mlukasek/SAPI_DTR-1/SW/PSoC_Creator/DTR-1 v2 HW.cydsn/codegentemp/AddrH.h

/*******************************************************************************
* File Name: AddrH.h  
* Version 2.20
*
* Description:
*  This file contains Pin function prototypes and register defines
*
* Note:
*
********************************************************************************
* Copyright 2008-2015, Cypress Semiconductor Corporation.  All rights reserved.
* You may use this file only in accordance with the license, terms, conditions, 
* disclaimers, and limitations in the end user license agreement accompanying 
* the software package with which this file was provided.
*******************************************************************************/

#if !defined(CY_PINS_AddrH_H) /* Pins AddrH_H */
#define CY_PINS_AddrH_H

#include "cytypes.h"
#include "cyfitter.h"
#include "cypins.h"
#include "AddrH_aliases.h"

/* APIs are not generated for P15[7:6] */
#if !(CY_PSOC5A &&\
	 AddrH__PORT == 15 && ((AddrH__MASK & 0xC0) != 0))


/***************************************
*        Function Prototypes             
***************************************/    

/**
* \addtogroup group_general
* @{
*/
void    AddrH_Write(uint8 value);
void    AddrH_SetDriveMode(uint8 mode);
uint8   AddrH_ReadDataReg(void);
uint8   AddrH_Read(void);
void    AddrH_SetInterruptMode(uint16 position, uint16 mode);
uint8   AddrH_ClearInterrupt(void);
/** @} general */

/***************************************
*           API Constants        
***************************************/
/**
* \addtogroup group_constants
* @{
*/
    /** \addtogroup driveMode Drive mode constants
     * \brief Constants to be passed as "mode" parameter in the AddrH_SetDriveMode() function.
     *  @{
     */
        #define AddrH_DM_ALG_HIZ         PIN_DM_ALG_HIZ
        #define AddrH_DM_DIG_HIZ         PIN_DM_DIG_HIZ
        #define AddrH_DM_RES_UP          PIN_DM_RES_UP
        #define AddrH_DM_RES_DWN         PIN_DM_RES_DWN
        #define AddrH_DM_OD_LO           PIN_DM_OD_LO
        #define AddrH_DM_OD_HI           PIN_DM_OD_HI
        #define AddrH_DM_STRONG          PIN_DM_STRONG
        #define AddrH_DM_RES_UPDWN       PIN_DM_RES_UPDWN
    /** @} driveMode */
/** @} group_constants */
    
/* Digital Port Constants */
#define AddrH_MASK               AddrH__MASK
#define AddrH_SHIFT              AddrH__SHIFT
#define AddrH_WIDTH              8u

/* Interrupt constants */
#if defined(AddrH__INTSTAT)
/**
* \addtogroup group_constants
* @{
*/
    /** \addtogroup intrMode Interrupt constants
     * \brief Constants to be passed as "mode" parameter in AddrH_SetInterruptMode() function.
     *  @{
     */
        #define AddrH_INTR_NONE      (uint16)(0x0000u)
        #define AddrH_INTR_RISING    (uint16)(0x0001u)
        #define AddrH_INTR_FALLING   (uint16)(0x0002u)
        #define AddrH_INTR_BOTH      (uint16)(0x0003u) 
    /** @} intrMode */
/** @} group_constants */

    #define AddrH_INTR_MASK      (0x01u) 
#endif /* (AddrH__INTSTAT) */


/***************************************
*             Registers        
***************************************/

/* Main Port Registers */
/* Pin State */
#define AddrH_PS                     (* (reg8 *) AddrH__PS)
/* Data Register */
#define AddrH_DR                     (* (reg8 *) AddrH__DR)
/* Port Number */
#define AddrH_PRT_NUM                (* (reg8 *) AddrH__PRT) 
/* Connect to Analog Globals */                                                  
#define AddrH_AG                     (* (reg8 *) AddrH__AG)                       
/* Analog MUX bux enable */
#define AddrH_AMUX                   (* (reg8 *) AddrH__AMUX) 
/* Bidirectional Enable */                                                        
#define AddrH_BIE                    (* (reg8 *) AddrH__BIE)
/* Bit-mask for Aliased Register Access */
#define AddrH_BIT_MASK               (* (reg8 *) AddrH__BIT_MASK)
/* Bypass Enable */
#define AddrH_BYP                    (* (reg8 *) AddrH__BYP)
/* Port wide control signals */                                                   
#define AddrH_CTL                    (* (reg8 *) AddrH__CTL)
/* Drive Modes */
#define AddrH_DM0                    (* (reg8 *) AddrH__DM0) 
#define AddrH_DM1                    (* (reg8 *) AddrH__DM1)
#define AddrH_DM2                    (* (reg8 *) AddrH__DM2) 
/* Input Buffer Disable Override */
#define AddrH_INP_DIS                (* (reg8 *) AddrH__INP_DIS)
/* LCD Common or Segment Drive */
#define AddrH_LCD_COM_SEG            (* (reg8 *) AddrH__LCD_COM_SEG)
/* Enable Segment LCD */
#define AddrH_LCD_EN                 (* (reg8 *) AddrH__LCD_EN)
/* Slew Rate Control */
#define AddrH_SLW                    (* (reg8 *) AddrH__SLW)

/* DSI Port Registers */
/* Global DSI Select Register */
#define AddrH_PRTDSI__CAPS_SEL       (* (reg8 *) AddrH__PRTDSI__CAPS_SEL) 
/* Double Sync Enable */
#define AddrH_PRTDSI__DBL_SYNC_IN    (* (reg8 *) AddrH__PRTDSI__DBL_SYNC_IN) 
/* Output Enable Select Drive Strength */
#define AddrH_PRTDSI__OE_SEL0        (* (reg8 *) AddrH__PRTDSI__OE_SEL0) 
#define AddrH_PRTDSI__OE_SEL1        (* (reg8 *) AddrH__PRTDSI__OE_SEL1) 
/* Port Pin Output Select Registers */
#define AddrH_PRTDSI__OUT_SEL0       (* (reg8 *) AddrH__PRTDSI__OUT_SEL0) 
#define AddrH_PRTDSI__OUT_SEL1       (* (reg8 *) AddrH__PRTDSI__OUT_SEL1) 
/* Sync Output Enable Registers */
#define AddrH_PRTDSI__SYNC_OUT       (* (reg8 *) AddrH__PRTDSI__SYNC_OUT) 

/* SIO registers */
#if defined(AddrH__SIO_CFG)
    #define AddrH_SIO_HYST_EN        (* (reg8 *) AddrH__SIO_HYST_EN)
    #define AddrH_SIO_REG_HIFREQ     (* (reg8 *) AddrH__SIO_REG_HIFREQ)
    #define AddrH_SIO_CFG            (* (reg8 *) AddrH__SIO_CFG)
    #define AddrH_SIO_DIFF           (* (reg8 *) AddrH__SIO_DIFF)
#endif /* (AddrH__SIO_CFG) */

/* Interrupt Registers */
#if defined(AddrH__INTSTAT)
    #define AddrH_INTSTAT            (* (reg8 *) AddrH__INTSTAT)
    #define AddrH_SNAP               (* (reg8 *) AddrH__SNAP)
    
	#define AddrH_0_INTTYPE_REG 		(* (reg8 *) AddrH__0__INTTYPE)
	#define AddrH_1_INTTYPE_REG 		(* (reg8 *) AddrH__1__INTTYPE)
	#define AddrH_2_INTTYPE_REG 		(* (reg8 *) AddrH__2__INTTYPE)
	#define AddrH_3_INTTYPE_REG 		(* (reg8 *) AddrH__3__INTTYPE)
	#define AddrH_4_INTTYPE_REG 		(* (reg8 *) AddrH__4__INTTYPE)
	#define AddrH_5_INTTYPE_REG 		(* (reg8 *) AddrH__5__INTTYPE)
	#define AddrH_6_INTTYPE_REG 		(* (reg8 *) AddrH__6__INTTYPE)
	#define AddrH_7_INTTYPE_REG 		(* (reg8 *) AddrH__7__INTTYPE)
#endif /* (AddrH__INTSTAT) */

#endif /* CY_PSOC5A... */

#endif /*  CY_PINS_AddrH_H */


/* [] END OF FILE */
