mlukasek/SAPI_DTR-1/SW/PSoC_Creator/DTR-1 v2 HW.cydsn/codegentemp/M1_Int.c

/*******************************************************************************
* File Name: M1_Int.c  
* Version 1.71
*
*  Description:
*   API for controlling the state of an interrupt.
*
*
*  Note:
*
********************************************************************************
* Copyright 2008-2015, Cypress Semiconductor Corporation.  All rights reserved.
* You may use this file only in accordance with the license, terms, conditions, 
* disclaimers, and limitations in the end user license agreement accompanying 
* the software package with which this file was provided.
*******************************************************************************/


#include <cydevice_trm.h>
#include <CyLib.h>
#include <M1_Int.h>
#include "cyapicallbacks.h"

#if !defined(M1_Int__REMOVED) /* Check for removal by optimization */

/*******************************************************************************
*  Place your includes, defines and code here 
********************************************************************************/
/* `#START M1_Int_intc` */

/* `#END` */

#ifndef CYINT_IRQ_BASE
#define CYINT_IRQ_BASE      16
#endif /* CYINT_IRQ_BASE */
#ifndef CYINT_VECT_TABLE
#define CYINT_VECT_TABLE    ((cyisraddress **) CYREG_NVIC_VECT_OFFSET)
#endif /* CYINT_VECT_TABLE */

/* Declared in startup, used to set unused interrupts to. */
CY_ISR_PROTO(IntDefaultHandler);


/*******************************************************************************
* Function Name: M1_Int_Start
********************************************************************************
*
* Summary:
*  Set up the interrupt and enable it. This function disables the interrupt, 
*  sets the default interrupt vector, sets the priority from the value in the
*  Design Wide Resources Interrupt Editor, then enables the interrupt to the 
*  interrupt controller.
*
* Parameters:  
*   None
*
* Return:
*   None
*
*******************************************************************************/
void M1_Int_Start(void)
{
    /* For all we know the interrupt is active. */
    M1_Int_Disable();

    /* Set the ISR to point to the M1_Int Interrupt. */
    M1_Int_SetVector(&M1_Int_Interrupt);

    /* Set the priority. */
    M1_Int_SetPriority((uint8)M1_Int_INTC_PRIOR_NUMBER);

    /* Enable it. */
    M1_Int_Enable();
}


/*******************************************************************************
* Function Name: M1_Int_StartEx
********************************************************************************
*
* Summary:
*  Sets up the interrupt and enables it. This function disables the interrupt,
*  sets the interrupt vector based on the address passed in, sets the priority 
*  from the value in the Design Wide Resources Interrupt Editor, then enables 
*  the interrupt to the interrupt controller.
*  
*  When defining ISR functions, the CY_ISR and CY_ISR_PROTO macros should be 
*  used to provide consistent definition across compilers:
*  
*  Function definition example:
*   CY_ISR(MyISR)
*   {
*   }
*   Function prototype example:
*   CY_ISR_PROTO(MyISR);
*
* Parameters:  
*   address: Address of the ISR to set in the interrupt vector table.
*
* Return:
*   None
*
*******************************************************************************/
void M1_Int_StartEx(cyisraddress address)
{
    /* For all we know the interrupt is active. */
    M1_Int_Disable();

    /* Set the ISR to point to the M1_Int Interrupt. */
    M1_Int_SetVector(address);

    /* Set the priority. */
    M1_Int_SetPriority((uint8)M1_Int_INTC_PRIOR_NUMBER);

    /* Enable it. */
    M1_Int_Enable();
}


/*******************************************************************************
* Function Name: M1_Int_Stop
********************************************************************************
*
* Summary:
*   Disables and removes the interrupt.
*
* Parameters:  
*   None
*
* Return:
*   None
*
*******************************************************************************/
void M1_Int_Stop(void)
{
    /* Disable this interrupt. */
    M1_Int_Disable();

    /* Set the ISR to point to the passive one. */
    M1_Int_SetVector(&IntDefaultHandler);
}


/*******************************************************************************
* Function Name: M1_Int_Interrupt
********************************************************************************
*
* Summary:
*   The default Interrupt Service Routine for M1_Int.
*
*   Add custom code between the coments to keep the next version of this file
*   from over writting your code.
*
* Parameters:  
*
* Return:
*   None
*
*******************************************************************************/
CY_ISR(M1_Int_Interrupt)
{
    #ifdef M1_Int_INTERRUPT_INTERRUPT_CALLBACK
        M1_Int_Interrupt_InterruptCallback();
    #endif /* M1_Int_INTERRUPT_INTERRUPT_CALLBACK */ 

    /*  Place your Interrupt code here. */
    /* `#START M1_Int_Interrupt` */

    /* `#END` */
}


/*******************************************************************************
* Function Name: M1_Int_SetVector
********************************************************************************
*
* Summary:
*   Change the ISR vector for the Interrupt. Note calling M1_Int_Start
*   will override any effect this method would have had. To set the vector 
*   before the component has been started use M1_Int_StartEx instead.
* 
*   When defining ISR functions, the CY_ISR and CY_ISR_PROTO macros should be 
*   used to provide consistent definition across compilers:
*
*   Function definition example:
*   CY_ISR(MyISR)
*   {
*   }
*
*   Function prototype example:
*     CY_ISR_PROTO(MyISR);
*
* Parameters:
*   address: Address of the ISR to set in the interrupt vector table.
*
* Return:
*   None
*
*******************************************************************************/
void M1_Int_SetVector(cyisraddress address)
{
    cyisraddress * ramVectorTable;

    ramVectorTable = (cyisraddress *) *CYINT_VECT_TABLE;

    ramVectorTable[CYINT_IRQ_BASE + (uint32)M1_Int__INTC_NUMBER] = address;
}


/*******************************************************************************
* Function Name: M1_Int_GetVector
********************************************************************************
*
* Summary:
*   Gets the "address" of the current ISR vector for the Interrupt.
*
* Parameters:
*   None
*
* Return:
*   Address of the ISR in the interrupt vector table.
*
*******************************************************************************/
cyisraddress M1_Int_GetVector(void)
{
    cyisraddress * ramVectorTable;

    ramVectorTable = (cyisraddress *) *CYINT_VECT_TABLE;

    return ramVectorTable[CYINT_IRQ_BASE + (uint32)M1_Int__INTC_NUMBER];
}


/*******************************************************************************
* Function Name: M1_Int_SetPriority
********************************************************************************
*
* Summary:
*   Sets the Priority of the Interrupt. 
*
*   Note calling M1_Int_Start or M1_Int_StartEx will 
*   override any effect this API would have had. This API should only be called
*   after M1_Int_Start or M1_Int_StartEx has been called. 
*   To set the initial priority for the component, use the Design-Wide Resources
*   Interrupt Editor.
*
*   Note This API has no effect on Non-maskable interrupt NMI).
*
* Parameters:
*   priority: Priority of the interrupt, 0 being the highest priority
*             PSoC 3 and PSoC 5LP: Priority is from 0 to 7.
*             PSoC 4: Priority is from 0 to 3.
*
* Return:
*   None
*
*******************************************************************************/
void M1_Int_SetPriority(uint8 priority)
{
    *M1_Int_INTC_PRIOR = priority << 5;
}


/*******************************************************************************
* Function Name: M1_Int_GetPriority
********************************************************************************
*
* Summary:
*   Gets the Priority of the Interrupt.
*
* Parameters:
*   None
*
* Return:
*   Priority of the interrupt, 0 being the highest priority
*    PSoC 3 and PSoC 5LP: Priority is from 0 to 7.
*    PSoC 4: Priority is from 0 to 3.
*
*******************************************************************************/
uint8 M1_Int_GetPriority(void)
{
    uint8 priority;


    priority = *M1_Int_INTC_PRIOR >> 5;

    return priority;
}


/*******************************************************************************
* Function Name: M1_Int_Enable
********************************************************************************
*
* Summary:
*   Enables the interrupt to the interrupt controller. Do not call this function
*   unless ISR_Start() has been called or the functionality of the ISR_Start() 
*   function, which sets the vector and the priority, has been called.
*
* Parameters:
*   None
*
* Return:
*   None
*
*******************************************************************************/
void M1_Int_Enable(void)
{
    /* Enable the general interrupt. */
    *M1_Int_INTC_SET_EN = M1_Int__INTC_MASK;
}


/*******************************************************************************
* Function Name: M1_Int_GetState
********************************************************************************
*
* Summary:
*   Gets the state (enabled, disabled) of the Interrupt.
*
* Parameters:
*   None
*
* Return:
*   1 if enabled, 0 if disabled.
*
*******************************************************************************/
uint8 M1_Int_GetState(void)
{
    /* Get the state of the general interrupt. */
    return ((*M1_Int_INTC_SET_EN & (uint32)M1_Int__INTC_MASK) != 0u) ? 1u:0u;
}


/*******************************************************************************
* Function Name: M1_Int_Disable
********************************************************************************
*
* Summary:
*   Disables the Interrupt in the interrupt controller.
*
* Parameters:
*   None
*
* Return:
*   None
*
*******************************************************************************/
void M1_Int_Disable(void)
{
    /* Disable the general interrupt. */
    *M1_Int_INTC_CLR_EN = M1_Int__INTC_MASK;
}


/*******************************************************************************
* Function Name: M1_Int_SetPending
********************************************************************************
*
* Summary:
*   Causes the Interrupt to enter the pending state, a software method of
*   generating the interrupt.
*
* Parameters:
*   None
*
* Return:
*   None
*
* Side Effects:
*   If interrupts are enabled and the interrupt is set up properly, the ISR is
*   entered (depending on the priority of this interrupt and other pending 
*   interrupts).
*
*******************************************************************************/
void M1_Int_SetPending(void)
{
    *M1_Int_INTC_SET_PD = M1_Int__INTC_MASK;
}


/*******************************************************************************
* Function Name: M1_Int_ClearPending
********************************************************************************
*
* Summary:
*   Clears a pending interrupt in the interrupt controller.
*
*   Note Some interrupt sources are clear-on-read and require the block 
*   interrupt/status register to be read/cleared with the appropriate block API 
*   (GPIO, UART, and so on). Otherwise the ISR will continue to remain in 
*   pending state even though the interrupt itself is cleared using this API.
*
* Parameters:
*   None
*
* Return:
*   None
*
*******************************************************************************/
void M1_Int_ClearPending(void)
{
    *M1_Int_INTC_CLR_PD = M1_Int__INTC_MASK;
}

#endif /* End check for removal by optimization */


/* [] END OF FILE */
