mlukasek/SAPI_DTR-1/SW/PSoC_Creator/DTR-1 v2 HW.cydsn/codegentemp/I2COLED_INT.c

/*******************************************************************************
* File Name: I2COLED_INT.c
* Version 3.50
*
* Description:
*  This file provides the source code of Interrupt Service Routine (ISR)
*  for the I2C component.
*
********************************************************************************
* Copyright 2008-2015, Cypress Semiconductor Corporation. All rights reserved.
* You may use this file only in accordance with the license, terms, conditions,
* disclaimers, and limitations in the end user license agreement accompanying
* the software package with which this file was provided.
*******************************************************************************/

#include "I2COLED_PVT.h"
#include "cyapicallbacks.h"


/*******************************************************************************
*  Place your includes, defines and code here.
********************************************************************************/
/* `#START I2COLED_ISR_intc` */

/* `#END` */


/*******************************************************************************
* Function Name: I2COLED_ISR
********************************************************************************
*
* Summary:
*  The handler for the I2C interrupt. The slave and master operations are
*  handled here.
*
* Parameters:
*  None.
*
* Return:
*  None.
*
* Reentrant:
*  No.
*
*******************************************************************************/
CY_ISR(I2COLED_ISR)
{
#if (I2COLED_MODE_SLAVE_ENABLED)
   uint8  tmp8;
#endif  /* (I2COLED_MODE_SLAVE_ENABLED) */

    uint8  tmpCsr;
    
#ifdef I2COLED_ISR_ENTRY_CALLBACK
    I2COLED_ISR_EntryCallback();
#endif /* I2COLED_ISR_ENTRY_CALLBACK */
    

#if(I2COLED_TIMEOUT_FF_ENABLED)
    if(0u != I2COLED_TimeoutGetStatus())
    {
        I2COLED_TimeoutReset();
        I2COLED_state = I2COLED_SM_EXIT_IDLE;
        /* I2COLED_CSR_REG should be cleared after reset */
    }
#endif /* (I2COLED_TIMEOUT_FF_ENABLED) */


    tmpCsr = I2COLED_CSR_REG;      /* Make copy as interrupts clear */

#if(I2COLED_MODE_MULTI_MASTER_SLAVE_ENABLED)
    if(I2COLED_CHECK_START_GEN(I2COLED_MCSR_REG))
    {
        I2COLED_CLEAR_START_GEN;

        /* Set transfer complete and error flags */
        I2COLED_mstrStatus |= (I2COLED_MSTAT_ERR_XFER |
                                        I2COLED_GET_MSTAT_CMPLT);

        /* Slave was addressed */
        I2COLED_state = I2COLED_SM_SLAVE;
    }
#endif /* (I2COLED_MODE_MULTI_MASTER_SLAVE_ENABLED) */


#if(I2COLED_MODE_MULTI_MASTER_ENABLED)
    if(I2COLED_CHECK_LOST_ARB(tmpCsr))
    {
        /* Set errors */
        I2COLED_mstrStatus |= (I2COLED_MSTAT_ERR_XFER     |
                                        I2COLED_MSTAT_ERR_ARB_LOST |
                                        I2COLED_GET_MSTAT_CMPLT);

        I2COLED_DISABLE_INT_ON_STOP; /* Interrupt on Stop is enabled by write */

        #if(I2COLED_MODE_MULTI_MASTER_SLAVE_ENABLED)
            if(I2COLED_CHECK_ADDRESS_STS(tmpCsr))
            {
                /* Slave was addressed */
                I2COLED_state = I2COLED_SM_SLAVE;
            }
            else
            {
                I2COLED_BUS_RELEASE;

                I2COLED_state = I2COLED_SM_EXIT_IDLE;
            }
        #else
            I2COLED_BUS_RELEASE;

            I2COLED_state = I2COLED_SM_EXIT_IDLE;

        #endif /* (I2COLED_MODE_MULTI_MASTER_SLAVE_ENABLED) */
    }
#endif /* (I2COLED_MODE_MULTI_MASTER_ENABLED) */

    /* Check for master operation mode */
    if(I2COLED_CHECK_SM_MASTER)
    {
    #if(I2COLED_MODE_MASTER_ENABLED)
        if(I2COLED_CHECK_BYTE_COMPLETE(tmpCsr))
        {
            switch (I2COLED_state)
            {
            case I2COLED_SM_MSTR_WR_ADDR:  /* After address is sent, write data */
            case I2COLED_SM_MSTR_RD_ADDR:  /* After address is sent, read data */

                tmpCsr &= ((uint8) ~I2COLED_CSR_STOP_STATUS); /* Clear Stop bit history on address phase */

                if(I2COLED_CHECK_ADDR_ACK(tmpCsr))
                {
                    /* Setup for transmit or receive of data */
                    if(I2COLED_state == I2COLED_SM_MSTR_WR_ADDR)   /* TRANSMIT data */
                    {
                        /* Check if at least one byte to transfer */
                        if(I2COLED_mstrWrBufSize > 0u)
                        {
                            /* Load the 1st data byte */
                            I2COLED_DATA_REG = I2COLED_mstrWrBufPtr[0u];
                            I2COLED_TRANSMIT_DATA;
                            I2COLED_mstrWrBufIndex = 1u;   /* Set index to 2nd element */

                            /* Set transmit state until done */
                            I2COLED_state = I2COLED_SM_MSTR_WR_DATA;
                        }
                        /* End of buffer: complete writing */
                        else if(I2COLED_CHECK_NO_STOP(I2COLED_mstrControl))
                        {
                            /* Set write complete and master halted */
                            I2COLED_mstrStatus |= (I2COLED_MSTAT_XFER_HALT |
                                                            I2COLED_MSTAT_WR_CMPLT);

                            I2COLED_state = I2COLED_SM_MSTR_HALT; /* Expect ReStart */
                            I2COLED_DisableInt();
                        }
                        else
                        {
                            I2COLED_ENABLE_INT_ON_STOP; /* Enable interrupt on Stop, to catch it */
                            I2COLED_GENERATE_STOP;
                        }
                    }
                    else  /* Master receive data */
                    {
                        I2COLED_READY_TO_READ; /* Release bus to read data */

                        I2COLED_state  = I2COLED_SM_MSTR_RD_DATA;
                    }
                }
                /* Address is NACKed */
                else if(I2COLED_CHECK_ADDR_NAK(tmpCsr))
                {
                    /* Set Address NAK error */
                    I2COLED_mstrStatus |= (I2COLED_MSTAT_ERR_XFER |
                                                    I2COLED_MSTAT_ERR_ADDR_NAK);

                    if(I2COLED_CHECK_NO_STOP(I2COLED_mstrControl))
                    {
                        I2COLED_mstrStatus |= (I2COLED_MSTAT_XFER_HALT |
                                                        I2COLED_GET_MSTAT_CMPLT);

                        I2COLED_state = I2COLED_SM_MSTR_HALT; /* Expect RESTART */
                        I2COLED_DisableInt();
                    }
                    else  /* Do normal Stop */
                    {
                        I2COLED_ENABLE_INT_ON_STOP; /* Enable interrupt on Stop, to catch it */
                        I2COLED_GENERATE_STOP;
                    }
                }
                else
                {
                    /* Address phase is not set for some reason: error */
                    #if(I2COLED_TIMEOUT_ENABLED)
                        /* Exit interrupt to take chance for timeout timer to handle this case */
                        I2COLED_DisableInt();
                        I2COLED_ClearPendingInt();
                    #else
                        /* Block execution flow: unexpected condition */
                        CYASSERT(0u != 0u);
                    #endif /* (I2COLED_TIMEOUT_ENABLED) */
                }
                break;

            case I2COLED_SM_MSTR_WR_DATA:

                if(I2COLED_CHECK_DATA_ACK(tmpCsr))
                {
                    /* Check if end of buffer */
                    if(I2COLED_mstrWrBufIndex  < I2COLED_mstrWrBufSize)
                    {
                        I2COLED_DATA_REG =
                                                 I2COLED_mstrWrBufPtr[I2COLED_mstrWrBufIndex];
                        I2COLED_TRANSMIT_DATA;
                        I2COLED_mstrWrBufIndex++;
                    }
                    /* End of buffer: complete writing */
                    else if(I2COLED_CHECK_NO_STOP(I2COLED_mstrControl))
                    {
                        /* Set write complete and master halted */
                        I2COLED_mstrStatus |= (I2COLED_MSTAT_XFER_HALT |
                                                        I2COLED_MSTAT_WR_CMPLT);

                        I2COLED_state = I2COLED_SM_MSTR_HALT;    /* Expect restart */
                        I2COLED_DisableInt();
                    }
                    else  /* Do normal Stop */
                    {
                        I2COLED_ENABLE_INT_ON_STOP;    /* Enable interrupt on Stop, to catch it */
                        I2COLED_GENERATE_STOP;
                    }
                }
                /* Last byte NAKed: end writing */
                else if(I2COLED_CHECK_NO_STOP(I2COLED_mstrControl))
                {
                    /* Set write complete, short transfer and master halted */
                    I2COLED_mstrStatus |= (I2COLED_MSTAT_ERR_XFER       |
                                                    I2COLED_MSTAT_ERR_SHORT_XFER |
                                                    I2COLED_MSTAT_XFER_HALT      |
                                                    I2COLED_MSTAT_WR_CMPLT);

                    I2COLED_state = I2COLED_SM_MSTR_HALT;    /* Expect ReStart */
                    I2COLED_DisableInt();
                }
                else  /* Do normal Stop */
                {
                    I2COLED_ENABLE_INT_ON_STOP;    /* Enable interrupt on Stop, to catch it */
                    I2COLED_GENERATE_STOP;

                    /* Set short transfer and error flag */
                    I2COLED_mstrStatus |= (I2COLED_MSTAT_ERR_SHORT_XFER |
                                                    I2COLED_MSTAT_ERR_XFER);
                }

                break;

            case I2COLED_SM_MSTR_RD_DATA:

                I2COLED_mstrRdBufPtr[I2COLED_mstrRdBufIndex] = I2COLED_DATA_REG;
                I2COLED_mstrRdBufIndex++;

                /* Check if end of buffer */
                if(I2COLED_mstrRdBufIndex < I2COLED_mstrRdBufSize)
                {
                    I2COLED_ACK_AND_RECEIVE;       /* ACK and receive byte */
                }
                /* End of buffer: complete reading */
                else if(I2COLED_CHECK_NO_STOP(I2COLED_mstrControl))
                {
                    /* Set read complete and master halted */
                    I2COLED_mstrStatus |= (I2COLED_MSTAT_XFER_HALT |
                                                    I2COLED_MSTAT_RD_CMPLT);

                    I2COLED_state = I2COLED_SM_MSTR_HALT;    /* Expect ReStart */
                    I2COLED_DisableInt();
                }
                else
                {
                    I2COLED_ENABLE_INT_ON_STOP;
                    I2COLED_NAK_AND_RECEIVE;       /* NACK and TRY to generate Stop */
                }
                break;

            default: /* This is an invalid state and should not occur */

            #if(I2COLED_TIMEOUT_ENABLED)
                /* Exit interrupt to take chance for timeout timer to handles this case */
                I2COLED_DisableInt();
                I2COLED_ClearPendingInt();
            #else
                /* Block execution flow: unexpected condition */
                CYASSERT(0u != 0u);
            #endif /* (I2COLED_TIMEOUT_ENABLED) */

                break;
            }
        }

        /* Catches Stop: end of transaction */
        if(I2COLED_CHECK_STOP_STS(tmpCsr))
        {
            I2COLED_mstrStatus |= I2COLED_GET_MSTAT_CMPLT;

            I2COLED_DISABLE_INT_ON_STOP;
            I2COLED_state = I2COLED_SM_IDLE;
        }
    #endif /* (I2COLED_MODE_MASTER_ENABLED) */
    }
    else if(I2COLED_CHECK_SM_SLAVE)
    {
    #if(I2COLED_MODE_SLAVE_ENABLED)

        if((I2COLED_CHECK_STOP_STS(tmpCsr)) || /* Stop || Restart */
           (I2COLED_CHECK_BYTE_COMPLETE(tmpCsr) && I2COLED_CHECK_ADDRESS_STS(tmpCsr)))
        {
            /* Catch end of master write transaction: use interrupt on Stop */
            /* The Stop bit history on address phase does not have correct state */
            if(I2COLED_SM_SL_WR_DATA == I2COLED_state)
            {
                I2COLED_DISABLE_INT_ON_STOP;

                I2COLED_slStatus &= ((uint8) ~I2COLED_SSTAT_WR_BUSY);
                I2COLED_slStatus |= ((uint8)  I2COLED_SSTAT_WR_CMPLT);

                I2COLED_state = I2COLED_SM_IDLE;
            }
        }

        if(I2COLED_CHECK_BYTE_COMPLETE(tmpCsr))
        {
            /* The address only issued after Start or ReStart: so check the address
               to catch these events:
                FF : sets an address phase with a byte_complete interrupt trigger.
                UDB: sets an address phase immediately after Start or ReStart. */
            if(I2COLED_CHECK_ADDRESS_STS(tmpCsr))
            {
            /* Check for software address detection */
            #if(I2COLED_SW_ADRR_DECODE)
                tmp8 = I2COLED_GET_SLAVE_ADDR(I2COLED_DATA_REG);

                if(tmp8 == I2COLED_slAddress)   /* Check for address match */
                {
                    if(0u != (I2COLED_DATA_REG & I2COLED_READ_FLAG))
                    {
                        /* Place code to prepare read buffer here                  */
                        /* `#START I2COLED_SW_PREPARE_READ_BUF_interrupt` */

                        /* `#END` */

                    #ifdef I2COLED_SW_PREPARE_READ_BUF_CALLBACK
                        I2COLED_SwPrepareReadBuf_Callback();
                    #endif /* I2COLED_SW_PREPARE_READ_BUF_CALLBACK */
                        
                        /* Prepare next operation to read, get data and place in data register */
                        if(I2COLED_slRdBufIndex < I2COLED_slRdBufSize)
                        {
                            /* Load first data byte from array */
                            I2COLED_DATA_REG = I2COLED_slRdBufPtr[I2COLED_slRdBufIndex];
                            I2COLED_ACK_AND_TRANSMIT;
                            I2COLED_slRdBufIndex++;

                            I2COLED_slStatus |= I2COLED_SSTAT_RD_BUSY;
                        }
                        else    /* Overflow: provide 0xFF on bus */
                        {
                            I2COLED_DATA_REG = I2COLED_OVERFLOW_RETURN;
                            I2COLED_ACK_AND_TRANSMIT;

                            I2COLED_slStatus  |= (I2COLED_SSTAT_RD_BUSY |
                                                           I2COLED_SSTAT_RD_ERR_OVFL);
                        }

                        I2COLED_state = I2COLED_SM_SL_RD_DATA;
                    }
                    else  /* Write transaction: receive 1st byte */
                    {
                        I2COLED_ACK_AND_RECEIVE;
                        I2COLED_state = I2COLED_SM_SL_WR_DATA;

                        I2COLED_slStatus |= I2COLED_SSTAT_WR_BUSY;
                        I2COLED_ENABLE_INT_ON_STOP;
                    }
                }
                else
                {
                    /*     Place code to compare for additional address here    */
                    /* `#START I2COLED_SW_ADDR_COMPARE_interruptStart` */

                    /* `#END` */

                #ifdef I2COLED_SW_ADDR_COMPARE_ENTRY_CALLBACK
                    I2COLED_SwAddrCompare_EntryCallback();
                #endif /* I2COLED_SW_ADDR_COMPARE_ENTRY_CALLBACK */
                    
                    I2COLED_NAK_AND_RECEIVE;   /* NACK address */

                    /* Place code to end of condition for NACK generation here */
                    /* `#START I2COLED_SW_ADDR_COMPARE_interruptEnd`  */

                    /* `#END` */

                #ifdef I2COLED_SW_ADDR_COMPARE_EXIT_CALLBACK
                    I2COLED_SwAddrCompare_ExitCallback();
                #endif /* I2COLED_SW_ADDR_COMPARE_EXIT_CALLBACK */
                }

            #else /* (I2COLED_HW_ADRR_DECODE) */

                if(0u != (I2COLED_DATA_REG & I2COLED_READ_FLAG))
                {
                    /* Place code to prepare read buffer here                  */
                    /* `#START I2COLED_HW_PREPARE_READ_BUF_interrupt` */

                    /* `#END` */
                    
                #ifdef I2COLED_HW_PREPARE_READ_BUF_CALLBACK
                    I2COLED_HwPrepareReadBuf_Callback();
                #endif /* I2COLED_HW_PREPARE_READ_BUF_CALLBACK */

                    /* Prepare next operation to read, get data and place in data register */
                    if(I2COLED_slRdBufIndex < I2COLED_slRdBufSize)
                    {
                        /* Load first data byte from array */
                        I2COLED_DATA_REG = I2COLED_slRdBufPtr[I2COLED_slRdBufIndex];
                        I2COLED_ACK_AND_TRANSMIT;
                        I2COLED_slRdBufIndex++;

                        I2COLED_slStatus |= I2COLED_SSTAT_RD_BUSY;
                    }
                    else    /* Overflow: provide 0xFF on bus */
                    {
                        I2COLED_DATA_REG = I2COLED_OVERFLOW_RETURN;
                        I2COLED_ACK_AND_TRANSMIT;

                        I2COLED_slStatus  |= (I2COLED_SSTAT_RD_BUSY |
                                                       I2COLED_SSTAT_RD_ERR_OVFL);
                    }

                    I2COLED_state = I2COLED_SM_SL_RD_DATA;
                }
                else  /* Write transaction: receive 1st byte */
                {
                    I2COLED_ACK_AND_RECEIVE;
                    I2COLED_state = I2COLED_SM_SL_WR_DATA;

                    I2COLED_slStatus |= I2COLED_SSTAT_WR_BUSY;
                    I2COLED_ENABLE_INT_ON_STOP;
                }

            #endif /* (I2COLED_SW_ADRR_DECODE) */
            }
            /* Data states */
            /* Data master writes into slave */
            else if(I2COLED_state == I2COLED_SM_SL_WR_DATA)
            {
                if(I2COLED_slWrBufIndex < I2COLED_slWrBufSize)
                {
                    tmp8 = I2COLED_DATA_REG;
                    I2COLED_ACK_AND_RECEIVE;
                    I2COLED_slWrBufPtr[I2COLED_slWrBufIndex] = tmp8;
                    I2COLED_slWrBufIndex++;
                }
                else  /* of array: complete write, send NACK */
                {
                    I2COLED_NAK_AND_RECEIVE;

                    I2COLED_slStatus |= I2COLED_SSTAT_WR_ERR_OVFL;
                }
            }
            /* Data master reads from slave */
            else if(I2COLED_state == I2COLED_SM_SL_RD_DATA)
            {
                if(I2COLED_CHECK_DATA_ACK(tmpCsr))
                {
                    if(I2COLED_slRdBufIndex < I2COLED_slRdBufSize)
                    {
                         /* Get data from array */
                        I2COLED_DATA_REG = I2COLED_slRdBufPtr[I2COLED_slRdBufIndex];
                        I2COLED_TRANSMIT_DATA;
                        I2COLED_slRdBufIndex++;
                    }
                    else   /* Overflow: provide 0xFF on bus */
                    {
                        I2COLED_DATA_REG = I2COLED_OVERFLOW_RETURN;
                        I2COLED_TRANSMIT_DATA;

                        I2COLED_slStatus |= I2COLED_SSTAT_RD_ERR_OVFL;
                    }
                }
                else  /* Last byte was NACKed: read complete */
                {
                    /* Only NACK appears on bus */
                    I2COLED_DATA_REG = I2COLED_OVERFLOW_RETURN;
                    I2COLED_NAK_AND_TRANSMIT;

                    I2COLED_slStatus &= ((uint8) ~I2COLED_SSTAT_RD_BUSY);
                    I2COLED_slStatus |= ((uint8)  I2COLED_SSTAT_RD_CMPLT);

                    I2COLED_state = I2COLED_SM_IDLE;
                }
            }
            else
            {
            #if(I2COLED_TIMEOUT_ENABLED)
                /* Exit interrupt to take chance for timeout timer to handle this case */
                I2COLED_DisableInt();
                I2COLED_ClearPendingInt();
            #else
                /* Block execution flow: unexpected condition */
                CYASSERT(0u != 0u);
            #endif /* (I2COLED_TIMEOUT_ENABLED) */
            }
        }
    #endif /* (I2COLED_MODE_SLAVE_ENABLED) */
    }
    else
    {
        /* The FSM skips master and slave processing: return to IDLE */
        I2COLED_state = I2COLED_SM_IDLE;
    }

#ifdef I2COLED_ISR_EXIT_CALLBACK
    I2COLED_ISR_ExitCallback();
#endif /* I2COLED_ISR_EXIT_CALLBACK */    
}


#if ((I2COLED_FF_IMPLEMENTED) && (I2COLED_WAKEUP_ENABLED))
    /*******************************************************************************
    * Function Name: I2COLED_WAKEUP_ISR
    ********************************************************************************
    *
    * Summary:
    *  The interrupt handler to trigger after a wakeup.
    *
    * Parameters:
    *  None.
    *
    * Return:
    *  None.
    *
    *******************************************************************************/
    CY_ISR(I2COLED_WAKEUP_ISR)
    {
    #ifdef I2COLED_WAKEUP_ISR_ENTRY_CALLBACK
        I2COLED_WAKEUP_ISR_EntryCallback();
    #endif /* I2COLED_WAKEUP_ISR_ENTRY_CALLBACK */
         
        /* Set flag to notify that matched address is received */
        I2COLED_wakeupSource = 1u;

        /* SCL is stretched until the I2C_Wake() is called */

    #ifdef I2COLED_WAKEUP_ISR_EXIT_CALLBACK
        I2COLED_WAKEUP_ISR_ExitCallback();
    #endif /* I2COLED_WAKEUP_ISR_EXIT_CALLBACK */
    }
#endif /* ((I2COLED_FF_IMPLEMENTED) && (I2COLED_WAKEUP_ENABLED)) */


/* [] END OF FILE */
