mlukasek/SAPI_DTR-1/SW/PSoC_Creator/DTR-1 v2 HW.cydsn/codegentemp/Millis.c

/*******************************************************************************
* File Name: Millis.c  
* Version 3.0
*
*  Description:
*     The Counter component consists of a 8, 16, 24 or 32-bit counter with
*     a selectable period between 2 and 2^Width - 1.  
*
*   Note:
*     None
*
********************************************************************************
* Copyright 2008-2012, Cypress Semiconductor Corporation.  All rights reserved.
* You may use this file only in accordance with the license, terms, conditions, 
* disclaimers, and limitations in the end user license agreement accompanying 
* the software package with which this file was provided.
*******************************************************************************/

#include "Millis.h"

uint8 Millis_initVar = 0u;


/*******************************************************************************
* Function Name: Millis_Init
********************************************************************************
* Summary:
*     Initialize to the schematic state
* 
* Parameters:  
*  void  
*
* Return: 
*  void
*
*******************************************************************************/
void Millis_Init(void) 
{
        #if (!Millis_UsingFixedFunction && !Millis_ControlRegRemoved)
            uint8 ctrl;
        #endif /* (!Millis_UsingFixedFunction && !Millis_ControlRegRemoved) */
        
        #if(!Millis_UsingFixedFunction) 
            /* Interrupt State Backup for Critical Region*/
            uint8 Millis_interruptState;
        #endif /* (!Millis_UsingFixedFunction) */
        
        #if (Millis_UsingFixedFunction)
            /* Clear all bits but the enable bit (if it's already set for Timer operation */
            Millis_CONTROL &= Millis_CTRL_ENABLE;
            
            /* Clear the mode bits for continuous run mode */
            #if (CY_PSOC5A)
                Millis_CONTROL2 &= ((uint8)(~Millis_CTRL_MODE_MASK));
            #endif /* (CY_PSOC5A) */
            #if (CY_PSOC3 || CY_PSOC5LP)
                Millis_CONTROL3 &= ((uint8)(~Millis_CTRL_MODE_MASK));                
            #endif /* (CY_PSOC3 || CY_PSOC5LP) */
            /* Check if One Shot mode is enabled i.e. RunMode !=0*/
            #if (Millis_RunModeUsed != 0x0u)
                /* Set 3rd bit of Control register to enable one shot mode */
                Millis_CONTROL |= Millis_ONESHOT;
            #endif /* (Millis_RunModeUsed != 0x0u) */
            
            /* Set the IRQ to use the status register interrupts */
            Millis_CONTROL2 |= Millis_CTRL2_IRQ_SEL;
            
            /* Clear and Set SYNCTC and SYNCCMP bits of RT1 register */
            Millis_RT1 &= ((uint8)(~Millis_RT1_MASK));
            Millis_RT1 |= Millis_SYNC;     
                    
            /*Enable DSI Sync all all inputs of the Timer*/
            Millis_RT1 &= ((uint8)(~Millis_SYNCDSI_MASK));
            Millis_RT1 |= Millis_SYNCDSI_EN;

        #else
            #if(!Millis_ControlRegRemoved)
            /* Set the default compare mode defined in the parameter */
            ctrl = Millis_CONTROL & ((uint8)(~Millis_CTRL_CMPMODE_MASK));
            Millis_CONTROL = ctrl | Millis_DEFAULT_COMPARE_MODE;
            
            /* Set the default capture mode defined in the parameter */
            ctrl = Millis_CONTROL & ((uint8)(~Millis_CTRL_CAPMODE_MASK));
            
            #if( 0 != Millis_CAPTURE_MODE_CONF)
                Millis_CONTROL = ctrl | Millis_DEFAULT_CAPTURE_MODE;
            #else
                Millis_CONTROL = ctrl;
            #endif /* 0 != Millis_CAPTURE_MODE */ 
            
            #endif /* (!Millis_ControlRegRemoved) */
        #endif /* (Millis_UsingFixedFunction) */
        
        /* Clear all data in the FIFO's */
        #if (!Millis_UsingFixedFunction)
            Millis_ClearFIFO();
        #endif /* (!Millis_UsingFixedFunction) */
        
        /* Set Initial values from Configuration */
        Millis_WritePeriod(Millis_INIT_PERIOD_VALUE);
        #if (!(Millis_UsingFixedFunction && (CY_PSOC5A)))
            Millis_WriteCounter(Millis_INIT_COUNTER_VALUE);
        #endif /* (!(Millis_UsingFixedFunction && (CY_PSOC5A))) */
        Millis_SetInterruptMode(Millis_INIT_INTERRUPTS_MASK);
        
        #if (!Millis_UsingFixedFunction)
            /* Read the status register to clear the unwanted interrupts */
            (void)Millis_ReadStatusRegister();
            /* Set the compare value (only available to non-fixed function implementation */
            Millis_WriteCompare(Millis_INIT_COMPARE_VALUE);
            /* Use the interrupt output of the status register for IRQ output */
            
            /* CyEnterCriticalRegion and CyExitCriticalRegion are used to mark following region critical*/
            /* Enter Critical Region*/
            Millis_interruptState = CyEnterCriticalSection();
            
            Millis_STATUS_AUX_CTRL |= Millis_STATUS_ACTL_INT_EN_MASK;
            
            /* Exit Critical Region*/
            CyExitCriticalSection(Millis_interruptState);
            
        #endif /* (!Millis_UsingFixedFunction) */
}


/*******************************************************************************
* Function Name: Millis_Enable
********************************************************************************
* Summary:
*     Enable the Counter
* 
* Parameters:  
*  void  
*
* Return: 
*  void
*
* Side Effects: 
*   If the Enable mode is set to Hardware only then this function has no effect 
*   on the operation of the counter.
*
*******************************************************************************/
void Millis_Enable(void) 
{
    /* Globally Enable the Fixed Function Block chosen */
    #if (Millis_UsingFixedFunction)
        Millis_GLOBAL_ENABLE |= Millis_BLOCK_EN_MASK;
        Millis_GLOBAL_STBY_ENABLE |= Millis_BLOCK_STBY_EN_MASK;
    #endif /* (Millis_UsingFixedFunction) */  
        
    /* Enable the counter from the control register  */
    /* If Fixed Function then make sure Mode is set correctly */
    /* else make sure reset is clear */
    #if(!Millis_ControlRegRemoved || Millis_UsingFixedFunction)
        Millis_CONTROL |= Millis_CTRL_ENABLE;                
    #endif /* (!Millis_ControlRegRemoved || Millis_UsingFixedFunction) */
    
}


/*******************************************************************************
* Function Name: Millis_Start
********************************************************************************
* Summary:
*  Enables the counter for operation 
*
* Parameters:  
*  void  
*
* Return: 
*  void
*
* Global variables:
*  Millis_initVar: Is modified when this function is called for the  
*   first time. Is used to ensure that initialization happens only once.
*
*******************************************************************************/
void Millis_Start(void) 
{
    if(Millis_initVar == 0u)
    {
        Millis_Init();
        
        Millis_initVar = 1u; /* Clear this bit for Initialization */        
    }
    
    /* Enable the Counter */
    Millis_Enable();        
}


/*******************************************************************************
* Function Name: Millis_Stop
********************************************************************************
* Summary:
* Halts the counter, but does not change any modes or disable interrupts.
*
* Parameters:  
*  void  
*
* Return: 
*  void
*
* Side Effects: If the Enable mode is set to Hardware only then this function
*               has no effect on the operation of the counter.
*
*******************************************************************************/
void Millis_Stop(void) 
{
    /* Disable Counter */
    #if(!Millis_ControlRegRemoved || Millis_UsingFixedFunction)
        Millis_CONTROL &= ((uint8)(~Millis_CTRL_ENABLE));        
    #endif /* (!Millis_ControlRegRemoved || Millis_UsingFixedFunction) */
    
    /* Globally disable the Fixed Function Block chosen */
    #if (Millis_UsingFixedFunction)
        Millis_GLOBAL_ENABLE &= ((uint8)(~Millis_BLOCK_EN_MASK));
        Millis_GLOBAL_STBY_ENABLE &= ((uint8)(~Millis_BLOCK_STBY_EN_MASK));
    #endif /* (Millis_UsingFixedFunction) */
}


/*******************************************************************************
* Function Name: Millis_SetInterruptMode
********************************************************************************
* Summary:
* Configures which interrupt sources are enabled to generate the final interrupt
*
* Parameters:  
*  InterruptsMask: This parameter is an or'd collection of the status bits
*                   which will be allowed to generate the counters interrupt.   
*
* Return: 
*  void
*
*******************************************************************************/
void Millis_SetInterruptMode(uint8 interruptsMask) 
{
    Millis_STATUS_MASK = interruptsMask;
}


/*******************************************************************************
* Function Name: Millis_ReadStatusRegister
********************************************************************************
* Summary:
*   Reads the status register and returns it's state. This function should use
*       defined types for the bit-field information as the bits in this
*       register may be permuteable.
*
* Parameters:  
*  void
*
* Return: 
*  (uint8) The contents of the status register
*
* Side Effects:
*   Status register bits may be clear on read. 
*
*******************************************************************************/
uint8   Millis_ReadStatusRegister(void) 
{
    return Millis_STATUS;
}


#if(!Millis_ControlRegRemoved)
/*******************************************************************************
* Function Name: Millis_ReadControlRegister
********************************************************************************
* Summary:
*   Reads the control register and returns it's state. This function should use
*       defined types for the bit-field information as the bits in this
*       register may be permuteable.
*
* Parameters:  
*  void
*
* Return: 
*  (uint8) The contents of the control register
*
*******************************************************************************/
uint8   Millis_ReadControlRegister(void) 
{
    return Millis_CONTROL;
}


/*******************************************************************************
* Function Name: Millis_WriteControlRegister
********************************************************************************
* Summary:
*   Sets the bit-field of the control register.  This function should use
*       defined types for the bit-field information as the bits in this
*       register may be permuteable.
*
* Parameters:  
*  void
*
* Return: 
*  (uint8) The contents of the control register
*
*******************************************************************************/
void    Millis_WriteControlRegister(uint8 control) 
{
    Millis_CONTROL = control;
}

#endif  /* (!Millis_ControlRegRemoved) */


#if (!(Millis_UsingFixedFunction && (CY_PSOC5A)))
/*******************************************************************************
* Function Name: Millis_WriteCounter
********************************************************************************
* Summary:
*   This funtion is used to set the counter to a specific value
*
* Parameters:  
*  counter:  New counter value. 
*
* Return: 
*  void 
*
*******************************************************************************/
void Millis_WriteCounter(uint32 counter) \
                                   
{
    #if(Millis_UsingFixedFunction)
        /* assert if block is already enabled */
        CYASSERT (0u == (Millis_GLOBAL_ENABLE & Millis_BLOCK_EN_MASK));
        /* If block is disabled, enable it and then write the counter */
        Millis_GLOBAL_ENABLE |= Millis_BLOCK_EN_MASK;
        CY_SET_REG16(Millis_COUNTER_LSB_PTR, (uint16)counter);
        Millis_GLOBAL_ENABLE &= ((uint8)(~Millis_BLOCK_EN_MASK));
    #else
        CY_SET_REG32(Millis_COUNTER_LSB_PTR, counter);
    #endif /* (Millis_UsingFixedFunction) */
}
#endif /* (!(Millis_UsingFixedFunction && (CY_PSOC5A))) */


/*******************************************************************************
* Function Name: Millis_ReadCounter
********************************************************************************
* Summary:
* Returns the current value of the counter.  It doesn't matter
* if the counter is enabled or running.
*
* Parameters:  
*  void:  
*
* Return: 
*  (uint32) The present value of the counter.
*
*******************************************************************************/
uint32 Millis_ReadCounter(void) 
{
    /* Force capture by reading Accumulator */
    /* Must first do a software capture to be able to read the counter */
    /* It is up to the user code to make sure there isn't already captured data in the FIFO */
    #if(Millis_UsingFixedFunction)
		(void)CY_GET_REG16(Millis_COUNTER_LSB_PTR);
	#else
		(void)CY_GET_REG8(Millis_COUNTER_LSB_PTR_8BIT);
	#endif/* (Millis_UsingFixedFunction) */
    
    /* Read the data from the FIFO (or capture register for Fixed Function)*/
    #if(Millis_UsingFixedFunction)
        return ((uint32)CY_GET_REG16(Millis_STATICCOUNT_LSB_PTR));
    #else
        return (CY_GET_REG32(Millis_STATICCOUNT_LSB_PTR));
    #endif /* (Millis_UsingFixedFunction) */
}


/*******************************************************************************
* Function Name: Millis_ReadCapture
********************************************************************************
* Summary:
*   This function returns the last value captured.
*
* Parameters:  
*  void
*
* Return: 
*  (uint32) Present Capture value.
*
*******************************************************************************/
uint32 Millis_ReadCapture(void) 
{
    #if(Millis_UsingFixedFunction)
        return ((uint32)CY_GET_REG16(Millis_STATICCOUNT_LSB_PTR));
    #else
        return (CY_GET_REG32(Millis_STATICCOUNT_LSB_PTR));
    #endif /* (Millis_UsingFixedFunction) */
}


/*******************************************************************************
* Function Name: Millis_WritePeriod
********************************************************************************
* Summary:
* Changes the period of the counter.  The new period 
* will be loaded the next time terminal count is detected.
*
* Parameters:  
*  period: (uint32) A value of 0 will result in
*         the counter remaining at zero.  
*
* Return: 
*  void
*
*******************************************************************************/
void Millis_WritePeriod(uint32 period) 
{
    #if(Millis_UsingFixedFunction)
        CY_SET_REG16(Millis_PERIOD_LSB_PTR,(uint16)period);
    #else
        CY_SET_REG32(Millis_PERIOD_LSB_PTR, period);
    #endif /* (Millis_UsingFixedFunction) */
}


/*******************************************************************************
* Function Name: Millis_ReadPeriod
********************************************************************************
* Summary:
* Reads the current period value without affecting counter operation.
*
* Parameters:  
*  void:  
*
* Return: 
*  (uint32) Present period value.
*
*******************************************************************************/
uint32 Millis_ReadPeriod(void) 
{
    #if(Millis_UsingFixedFunction)
        return ((uint32)CY_GET_REG16(Millis_PERIOD_LSB_PTR));
    #else
        return (CY_GET_REG32(Millis_PERIOD_LSB_PTR));
    #endif /* (Millis_UsingFixedFunction) */
}


#if (!Millis_UsingFixedFunction)
/*******************************************************************************
* Function Name: Millis_WriteCompare
********************************************************************************
* Summary:
* Changes the compare value.  The compare output will 
* reflect the new value on the next UDB clock.  The compare output will be 
* driven high when the present counter value compares true based on the 
* configured compare mode setting. 
*
* Parameters:  
*  Compare:  New compare value. 
*
* Return: 
*  void
*
*******************************************************************************/
void Millis_WriteCompare(uint32 compare) \
                                   
{
    #if(Millis_UsingFixedFunction)
        CY_SET_REG16(Millis_COMPARE_LSB_PTR, (uint16)compare);
    #else
        CY_SET_REG32(Millis_COMPARE_LSB_PTR, compare);
    #endif /* (Millis_UsingFixedFunction) */
}


/*******************************************************************************
* Function Name: Millis_ReadCompare
********************************************************************************
* Summary:
* Returns the compare value.
*
* Parameters:  
*  void:
*
* Return: 
*  (uint32) Present compare value.
*
*******************************************************************************/
uint32 Millis_ReadCompare(void) 
{
    return (CY_GET_REG32(Millis_COMPARE_LSB_PTR));
}


#if (Millis_COMPARE_MODE_SOFTWARE)
/*******************************************************************************
* Function Name: Millis_SetCompareMode
********************************************************************************
* Summary:
*  Sets the software controlled Compare Mode.
*
* Parameters:
*  compareMode:  Compare Mode Enumerated Type.
*
* Return:
*  void
*
*******************************************************************************/
void Millis_SetCompareMode(uint8 compareMode) 
{
    /* Clear the compare mode bits in the control register */
    Millis_CONTROL &= ((uint8)(~Millis_CTRL_CMPMODE_MASK));
    
    /* Write the new setting */
    Millis_CONTROL |= compareMode;
}
#endif  /* (Millis_COMPARE_MODE_SOFTWARE) */


#if (Millis_CAPTURE_MODE_SOFTWARE)
/*******************************************************************************
* Function Name: Millis_SetCaptureMode
********************************************************************************
* Summary:
*  Sets the software controlled Capture Mode.
*
* Parameters:
*  captureMode:  Capture Mode Enumerated Type.
*
* Return:
*  void
*
*******************************************************************************/
void Millis_SetCaptureMode(uint8 captureMode) 
{
    /* Clear the capture mode bits in the control register */
    Millis_CONTROL &= ((uint8)(~Millis_CTRL_CAPMODE_MASK));
    
    /* Write the new setting */
    Millis_CONTROL |= ((uint8)((uint8)captureMode << Millis_CTRL_CAPMODE0_SHIFT));
}
#endif  /* (Millis_CAPTURE_MODE_SOFTWARE) */


/*******************************************************************************
* Function Name: Millis_ClearFIFO
********************************************************************************
* Summary:
*   This function clears all capture data from the capture FIFO
*
* Parameters:  
*  void:
*
* Return: 
*  None
*
*******************************************************************************/
void Millis_ClearFIFO(void) 
{

    while(0u != (Millis_ReadStatusRegister() & Millis_STATUS_FIFONEMP))
    {
        (void)Millis_ReadCapture();
    }

}
#endif  /* (!Millis_UsingFixedFunction) */


/* [] END OF FILE */
