mlukasek/SAPI_DTR-1/SW/PSoC_Creator/DTR-1 v2 HW.cydsn/codegentemp/Millis.h

/*******************************************************************************
* File Name: Millis.h  
* Version 3.0
*
*  Description:
*   Contains the function prototypes and constants available to the counter
*   user module.
*
*   Note:
*    None
*
********************************************************************************
* Copyright 2008-2015, Cypress Semiconductor Corporation.  All rights reserved.
* You may use this file only in accordance with the license, terms, conditions, 
* disclaimers, and limitations in the end user license agreement accompanying 
* the software package with which this file was provided.
*******************************************************************************/
    
#if !defined(CY_COUNTER_Millis_H)
#define CY_COUNTER_Millis_H

#include "cytypes.h"
#include "cyfitter.h"
#include "CyLib.h" /* For CyEnterCriticalSection() and CyExitCriticalSection() functions */

extern uint8 Millis_initVar;

/* Check to see if required defines such as CY_PSOC5LP are available */
/* They are defined starting with cy_boot v3.0 */
#if !defined (CY_PSOC5LP)
    #error Component Counter_v3_0 requires cy_boot v3.0 or later
#endif /* (CY_ PSOC5LP) */

/* Error message for removed Millis_CounterUDB_sCTRLReg_ctrlreg through optimization */
#ifdef Millis_CounterUDB_sCTRLReg_ctrlreg__REMOVED
    #error Counter_v3_0 detected with a constant 0 for the enable, a \
                                constant 0 for the count or constant 1 for \
                                the reset. This will prevent the component from\
                                operating.
#endif /* Millis_CounterUDB_sCTRLReg_ctrlreg__REMOVED */


/**************************************
*           Parameter Defaults        
**************************************/

#define Millis_Resolution            32u
#define Millis_UsingFixedFunction    0u
#define Millis_ControlRegRemoved     1u
#define Millis_COMPARE_MODE_SOFTWARE 0u
#define Millis_CAPTURE_MODE_SOFTWARE 0u
#define Millis_RunModeUsed           0u


/***************************************
*       Type defines
***************************************/


/**************************************************************************
 * Sleep Mode API Support
 * Backup structure for Sleep Wake up operations
 *************************************************************************/
typedef struct
{
    uint8 CounterEnableState; 
    uint32 CounterUdb;         /* Current Counter Value */

    #if (!Millis_ControlRegRemoved)
        uint8 CounterControlRegister;               /* Counter Control Register */
    #endif /* (!Millis_ControlRegRemoved) */

}Millis_backupStruct;


/**************************************
 *  Function Prototypes
 *************************************/
void    Millis_Start(void) ;
void    Millis_Stop(void) ;
void    Millis_SetInterruptMode(uint8 interruptsMask) ;
uint8   Millis_ReadStatusRegister(void) ;
#define Millis_GetInterruptSource() Millis_ReadStatusRegister()
#if(!Millis_ControlRegRemoved)
    uint8   Millis_ReadControlRegister(void) ;
    void    Millis_WriteControlRegister(uint8 control) \
        ;
#endif /* (!Millis_ControlRegRemoved) */
#if (!(Millis_UsingFixedFunction && (CY_PSOC5A)))
    void    Millis_WriteCounter(uint32 counter) \
            ; 
#endif /* (!(Millis_UsingFixedFunction && (CY_PSOC5A))) */
uint32  Millis_ReadCounter(void) ;
uint32  Millis_ReadCapture(void) ;
void    Millis_WritePeriod(uint32 period) \
    ;
uint32  Millis_ReadPeriod( void ) ;
#if (!Millis_UsingFixedFunction)
    void    Millis_WriteCompare(uint32 compare) \
        ;
    uint32  Millis_ReadCompare( void ) \
        ;
#endif /* (!Millis_UsingFixedFunction) */

#if (Millis_COMPARE_MODE_SOFTWARE)
    void    Millis_SetCompareMode(uint8 compareMode) ;
#endif /* (Millis_COMPARE_MODE_SOFTWARE) */
#if (Millis_CAPTURE_MODE_SOFTWARE)
    void    Millis_SetCaptureMode(uint8 captureMode) ;
#endif /* (Millis_CAPTURE_MODE_SOFTWARE) */
void Millis_ClearFIFO(void)     ;
void Millis_Init(void)          ;
void Millis_Enable(void)        ;
void Millis_SaveConfig(void)    ;
void Millis_RestoreConfig(void) ;
void Millis_Sleep(void)         ;
void Millis_Wakeup(void)        ;


/***************************************
*   Enumerated Types and Parameters
***************************************/

/* Enumerated Type B_Counter__CompareModes, Used in Compare Mode retained for backward compatibility of tests*/
#define Millis__B_COUNTER__LESS_THAN 1
#define Millis__B_COUNTER__LESS_THAN_OR_EQUAL 2
#define Millis__B_COUNTER__EQUAL 0
#define Millis__B_COUNTER__GREATER_THAN 3
#define Millis__B_COUNTER__GREATER_THAN_OR_EQUAL 4
#define Millis__B_COUNTER__SOFTWARE 5

/* Enumerated Type Counter_CompareModes */
#define Millis_CMP_MODE_LT 1u
#define Millis_CMP_MODE_LTE 2u
#define Millis_CMP_MODE_EQ 0u
#define Millis_CMP_MODE_GT 3u
#define Millis_CMP_MODE_GTE 4u
#define Millis_CMP_MODE_SOFTWARE_CONTROLLED 5u

/* Enumerated Type B_Counter__CaptureModes, Used in Capture Mode retained for backward compatibility of tests*/
#define Millis__B_COUNTER__NONE 0
#define Millis__B_COUNTER__RISING_EDGE 1
#define Millis__B_COUNTER__FALLING_EDGE 2
#define Millis__B_COUNTER__EITHER_EDGE 3
#define Millis__B_COUNTER__SOFTWARE_CONTROL 4

/* Enumerated Type Counter_CompareModes */
#define Millis_CAP_MODE_NONE 0u
#define Millis_CAP_MODE_RISE 1u
#define Millis_CAP_MODE_FALL 2u
#define Millis_CAP_MODE_BOTH 3u
#define Millis_CAP_MODE_SOFTWARE_CONTROLLED 4u


/***************************************
 *  Initialization Values
 **************************************/
#define Millis_CAPTURE_MODE_CONF       0u
#define Millis_INIT_PERIOD_VALUE       4294967294u
#define Millis_INIT_COUNTER_VALUE      0u
#if (Millis_UsingFixedFunction)
#define Millis_INIT_INTERRUPTS_MASK    ((uint8)((uint8)0u << Millis_STATUS_ZERO_INT_EN_MASK_SHIFT))
#else
#define Millis_INIT_COMPARE_VALUE      4294967294u
#define Millis_INIT_INTERRUPTS_MASK ((uint8)((uint8)0u << Millis_STATUS_ZERO_INT_EN_MASK_SHIFT) | \
        ((uint8)((uint8)0u << Millis_STATUS_CAPTURE_INT_EN_MASK_SHIFT)) | \
        ((uint8)((uint8)0u << Millis_STATUS_CMP_INT_EN_MASK_SHIFT)) | \
        ((uint8)((uint8)0u << Millis_STATUS_OVERFLOW_INT_EN_MASK_SHIFT)) | \
        ((uint8)((uint8)0u << Millis_STATUS_UNDERFLOW_INT_EN_MASK_SHIFT)))
#define Millis_DEFAULT_COMPARE_MODE    1u

#if( 0 != Millis_CAPTURE_MODE_CONF)
    #define Millis_DEFAULT_CAPTURE_MODE    ((uint8)((uint8)0u << Millis_CTRL_CAPMODE0_SHIFT))
#else    
    #define Millis_DEFAULT_CAPTURE_MODE    (0u )
#endif /* ( 0 != Millis_CAPTURE_MODE_CONF) */

#endif /* (Millis_UsingFixedFunction) */


/**************************************
 *  Registers
 *************************************/
#if (Millis_UsingFixedFunction)
    #define Millis_STATICCOUNT_LSB     (*(reg16 *) Millis_CounterHW__CAP0 )
    #define Millis_STATICCOUNT_LSB_PTR ( (reg16 *) Millis_CounterHW__CAP0 )
    #define Millis_PERIOD_LSB          (*(reg16 *) Millis_CounterHW__PER0 )
    #define Millis_PERIOD_LSB_PTR      ( (reg16 *) Millis_CounterHW__PER0 )
    /* MODE must be set to 1 to set the compare value */
    #define Millis_COMPARE_LSB         (*(reg16 *) Millis_CounterHW__CNT_CMP0 )
    #define Millis_COMPARE_LSB_PTR     ( (reg16 *) Millis_CounterHW__CNT_CMP0 )
    /* MODE must be set to 0 to get the count */
    #define Millis_COUNTER_LSB         (*(reg16 *) Millis_CounterHW__CNT_CMP0 )
    #define Millis_COUNTER_LSB_PTR     ( (reg16 *) Millis_CounterHW__CNT_CMP0 )
    #define Millis_RT1                 (*(reg8 *) Millis_CounterHW__RT1)
    #define Millis_RT1_PTR             ( (reg8 *) Millis_CounterHW__RT1)
#else
    
    #if (Millis_Resolution <= 8u) /* 8-bit Counter */
    
        #define Millis_STATICCOUNT_LSB     (*(reg8 *) \
            Millis_CounterUDB_sC32_counterdp_u0__F0_REG )
        #define Millis_STATICCOUNT_LSB_PTR ( (reg8 *) \
            Millis_CounterUDB_sC32_counterdp_u0__F0_REG )
        #define Millis_PERIOD_LSB          (*(reg8 *) \
            Millis_CounterUDB_sC32_counterdp_u0__D0_REG )
        #define Millis_PERIOD_LSB_PTR      ( (reg8 *) \
            Millis_CounterUDB_sC32_counterdp_u0__D0_REG )
        #define Millis_COMPARE_LSB         (*(reg8 *) \
            Millis_CounterUDB_sC32_counterdp_u0__D1_REG )
        #define Millis_COMPARE_LSB_PTR     ( (reg8 *) \
            Millis_CounterUDB_sC32_counterdp_u0__D1_REG )
        #define Millis_COUNTER_LSB         (*(reg8 *) \
            Millis_CounterUDB_sC32_counterdp_u0__A0_REG )  
        #define Millis_COUNTER_LSB_PTR     ( (reg8 *)\
            Millis_CounterUDB_sC32_counterdp_u0__A0_REG )
    
    #elif(Millis_Resolution <= 16u) /* 16-bit Counter */
        #if(CY_PSOC3) /* 8-bit address space */ 
            #define Millis_STATICCOUNT_LSB     (*(reg16 *) \
                Millis_CounterUDB_sC32_counterdp_u0__F0_REG )
            #define Millis_STATICCOUNT_LSB_PTR ( (reg16 *) \
                Millis_CounterUDB_sC32_counterdp_u0__F0_REG )
            #define Millis_PERIOD_LSB          (*(reg16 *) \
                Millis_CounterUDB_sC32_counterdp_u0__D0_REG )
            #define Millis_PERIOD_LSB_PTR      ( (reg16 *) \
                Millis_CounterUDB_sC32_counterdp_u0__D0_REG )
            #define Millis_COMPARE_LSB         (*(reg16 *) \
                Millis_CounterUDB_sC32_counterdp_u0__D1_REG )
            #define Millis_COMPARE_LSB_PTR     ( (reg16 *) \
                Millis_CounterUDB_sC32_counterdp_u0__D1_REG )
            #define Millis_COUNTER_LSB         (*(reg16 *) \
                Millis_CounterUDB_sC32_counterdp_u0__A0_REG )  
            #define Millis_COUNTER_LSB_PTR     ( (reg16 *)\
                Millis_CounterUDB_sC32_counterdp_u0__A0_REG )
        #else /* 16-bit address space */
            #define Millis_STATICCOUNT_LSB     (*(reg16 *) \
                Millis_CounterUDB_sC32_counterdp_u0__16BIT_F0_REG )
            #define Millis_STATICCOUNT_LSB_PTR ( (reg16 *) \
                Millis_CounterUDB_sC32_counterdp_u0__16BIT_F0_REG )
            #define Millis_PERIOD_LSB          (*(reg16 *) \
                Millis_CounterUDB_sC32_counterdp_u0__16BIT_D0_REG )
            #define Millis_PERIOD_LSB_PTR      ( (reg16 *) \
                Millis_CounterUDB_sC32_counterdp_u0__16BIT_D0_REG )
            #define Millis_COMPARE_LSB         (*(reg16 *) \
                Millis_CounterUDB_sC32_counterdp_u0__16BIT_D1_REG )
            #define Millis_COMPARE_LSB_PTR     ( (reg16 *) \
                Millis_CounterUDB_sC32_counterdp_u0__16BIT_D1_REG )
            #define Millis_COUNTER_LSB         (*(reg16 *) \
                Millis_CounterUDB_sC32_counterdp_u0__16BIT_A0_REG )  
            #define Millis_COUNTER_LSB_PTR     ( (reg16 *)\
                Millis_CounterUDB_sC32_counterdp_u0__16BIT_A0_REG )
        #endif /* CY_PSOC3 */   
    #elif(Millis_Resolution <= 24u) /* 24-bit Counter */
        
        #define Millis_STATICCOUNT_LSB     (*(reg32 *) \
            Millis_CounterUDB_sC32_counterdp_u0__F0_REG )
        #define Millis_STATICCOUNT_LSB_PTR ( (reg32 *) \
            Millis_CounterUDB_sC32_counterdp_u0__F0_REG )
        #define Millis_PERIOD_LSB          (*(reg32 *) \
            Millis_CounterUDB_sC32_counterdp_u0__D0_REG )
        #define Millis_PERIOD_LSB_PTR      ( (reg32 *) \
            Millis_CounterUDB_sC32_counterdp_u0__D0_REG )
        #define Millis_COMPARE_LSB         (*(reg32 *) \
            Millis_CounterUDB_sC32_counterdp_u0__D1_REG )
        #define Millis_COMPARE_LSB_PTR     ( (reg32 *) \
            Millis_CounterUDB_sC32_counterdp_u0__D1_REG )
        #define Millis_COUNTER_LSB         (*(reg32 *) \
            Millis_CounterUDB_sC32_counterdp_u0__A0_REG )  
        #define Millis_COUNTER_LSB_PTR     ( (reg32 *)\
            Millis_CounterUDB_sC32_counterdp_u0__A0_REG )
    
    #else /* 32-bit Counter */
        #if(CY_PSOC3 || CY_PSOC5) /* 8-bit address space */
            #define Millis_STATICCOUNT_LSB     (*(reg32 *) \
                Millis_CounterUDB_sC32_counterdp_u0__F0_REG )
            #define Millis_STATICCOUNT_LSB_PTR ( (reg32 *) \
                Millis_CounterUDB_sC32_counterdp_u0__F0_REG )
            #define Millis_PERIOD_LSB          (*(reg32 *) \
                Millis_CounterUDB_sC32_counterdp_u0__D0_REG )
            #define Millis_PERIOD_LSB_PTR      ( (reg32 *) \
                Millis_CounterUDB_sC32_counterdp_u0__D0_REG )
            #define Millis_COMPARE_LSB         (*(reg32 *) \
                Millis_CounterUDB_sC32_counterdp_u0__D1_REG )
            #define Millis_COMPARE_LSB_PTR     ( (reg32 *) \
                Millis_CounterUDB_sC32_counterdp_u0__D1_REG )
            #define Millis_COUNTER_LSB         (*(reg32 *) \
                Millis_CounterUDB_sC32_counterdp_u0__A0_REG )  
            #define Millis_COUNTER_LSB_PTR     ( (reg32 *)\
                Millis_CounterUDB_sC32_counterdp_u0__A0_REG )
        #else /* 32-bit address space */
            #define Millis_STATICCOUNT_LSB     (*(reg32 *) \
                Millis_CounterUDB_sC32_counterdp_u0__32BIT_F0_REG )
            #define Millis_STATICCOUNT_LSB_PTR ( (reg32 *) \
                Millis_CounterUDB_sC32_counterdp_u0__32BIT_F0_REG )
            #define Millis_PERIOD_LSB          (*(reg32 *) \
                Millis_CounterUDB_sC32_counterdp_u0__32BIT_D0_REG )
            #define Millis_PERIOD_LSB_PTR      ( (reg32 *) \
                Millis_CounterUDB_sC32_counterdp_u0__32BIT_D0_REG )
            #define Millis_COMPARE_LSB         (*(reg32 *) \
                Millis_CounterUDB_sC32_counterdp_u0__32BIT_D1_REG )
            #define Millis_COMPARE_LSB_PTR     ( (reg32 *) \
                Millis_CounterUDB_sC32_counterdp_u0__32BIT_D1_REG )
            #define Millis_COUNTER_LSB         (*(reg32 *) \
                Millis_CounterUDB_sC32_counterdp_u0__32BIT_A0_REG )  
            #define Millis_COUNTER_LSB_PTR     ( (reg32 *)\
                Millis_CounterUDB_sC32_counterdp_u0__32BIT_A0_REG )
        #endif /* CY_PSOC3 || CY_PSOC5 */   
    #endif

	#define Millis_COUNTER_LSB_PTR_8BIT     ( (reg8 *)\
                Millis_CounterUDB_sC32_counterdp_u0__A0_REG )
				
    #define Millis_AUX_CONTROLDP0 \
        (*(reg8 *) Millis_CounterUDB_sC32_counterdp_u0__DP_AUX_CTL_REG)
    
    #define Millis_AUX_CONTROLDP0_PTR \
        ( (reg8 *) Millis_CounterUDB_sC32_counterdp_u0__DP_AUX_CTL_REG)
    
    #if (Millis_Resolution == 16 || Millis_Resolution == 24 || Millis_Resolution == 32)
       #define Millis_AUX_CONTROLDP1 \
           (*(reg8 *) Millis_CounterUDB_sC32_counterdp_u1__DP_AUX_CTL_REG)
       #define Millis_AUX_CONTROLDP1_PTR \
           ( (reg8 *) Millis_CounterUDB_sC32_counterdp_u1__DP_AUX_CTL_REG)
    #endif /* (Millis_Resolution == 16 || Millis_Resolution == 24 || Millis_Resolution == 32) */
    
    #if (Millis_Resolution == 24 || Millis_Resolution == 32)
       #define Millis_AUX_CONTROLDP2 \
           (*(reg8 *) Millis_CounterUDB_sC32_counterdp_u2__DP_AUX_CTL_REG)
       #define Millis_AUX_CONTROLDP2_PTR \
           ( (reg8 *) Millis_CounterUDB_sC32_counterdp_u2__DP_AUX_CTL_REG)
    #endif /* (Millis_Resolution == 24 || Millis_Resolution == 32) */
    
    #if (Millis_Resolution == 32)
       #define Millis_AUX_CONTROLDP3 \
           (*(reg8 *) Millis_CounterUDB_sC32_counterdp_u3__DP_AUX_CTL_REG)
       #define Millis_AUX_CONTROLDP3_PTR \
           ( (reg8 *) Millis_CounterUDB_sC32_counterdp_u3__DP_AUX_CTL_REG)
    #endif /* (Millis_Resolution == 32) */

#endif  /* (Millis_UsingFixedFunction) */

#if (Millis_UsingFixedFunction)
    #define Millis_STATUS         (*(reg8 *) Millis_CounterHW__SR0 )
    /* In Fixed Function Block Status and Mask are the same register */
    #define Millis_STATUS_MASK             (*(reg8 *) Millis_CounterHW__SR0 )
    #define Millis_STATUS_MASK_PTR         ( (reg8 *) Millis_CounterHW__SR0 )
    #define Millis_CONTROL                 (*(reg8 *) Millis_CounterHW__CFG0)
    #define Millis_CONTROL_PTR             ( (reg8 *) Millis_CounterHW__CFG0)
    #define Millis_CONTROL2                (*(reg8 *) Millis_CounterHW__CFG1)
    #define Millis_CONTROL2_PTR            ( (reg8 *) Millis_CounterHW__CFG1)
    #if (CY_PSOC3 || CY_PSOC5LP)
        #define Millis_CONTROL3       (*(reg8 *) Millis_CounterHW__CFG2)
        #define Millis_CONTROL3_PTR   ( (reg8 *) Millis_CounterHW__CFG2)
    #endif /* (CY_PSOC3 || CY_PSOC5LP) */
    #define Millis_GLOBAL_ENABLE           (*(reg8 *) Millis_CounterHW__PM_ACT_CFG)
    #define Millis_GLOBAL_ENABLE_PTR       ( (reg8 *) Millis_CounterHW__PM_ACT_CFG)
    #define Millis_GLOBAL_STBY_ENABLE      (*(reg8 *) Millis_CounterHW__PM_STBY_CFG)
    #define Millis_GLOBAL_STBY_ENABLE_PTR  ( (reg8 *) Millis_CounterHW__PM_STBY_CFG)
    

    /********************************
    *    Constants
    ********************************/

    /* Fixed Function Block Chosen */
    #define Millis_BLOCK_EN_MASK          Millis_CounterHW__PM_ACT_MSK
    #define Millis_BLOCK_STBY_EN_MASK     Millis_CounterHW__PM_STBY_MSK 
    
    /* Control Register Bit Locations */    
    /* As defined in Register Map, part of TMRX_CFG0 register */
    #define Millis_CTRL_ENABLE_SHIFT      0x00u
    #define Millis_ONESHOT_SHIFT          0x02u
    /* Control Register Bit Masks */
    #define Millis_CTRL_ENABLE            ((uint8)((uint8)0x01u << Millis_CTRL_ENABLE_SHIFT))         
    #define Millis_ONESHOT                ((uint8)((uint8)0x01u << Millis_ONESHOT_SHIFT))

    /* Control2 Register Bit Masks */
    /* Set the mask for run mode */
    #if (CY_PSOC5A)
        /* Use CFG1 Mode bits to set run mode */
        #define Millis_CTRL_MODE_SHIFT        0x01u    
        #define Millis_CTRL_MODE_MASK         ((uint8)((uint8)0x07u << Millis_CTRL_MODE_SHIFT))
    #endif /* (CY_PSOC5A) */
    #if (CY_PSOC3 || CY_PSOC5LP)
        /* Use CFG2 Mode bits to set run mode */
        #define Millis_CTRL_MODE_SHIFT        0x00u    
        #define Millis_CTRL_MODE_MASK         ((uint8)((uint8)0x03u << Millis_CTRL_MODE_SHIFT))
    #endif /* (CY_PSOC3 || CY_PSOC5LP) */
    /* Set the mask for interrupt (raw/status register) */
    #define Millis_CTRL2_IRQ_SEL_SHIFT     0x00u
    #define Millis_CTRL2_IRQ_SEL          ((uint8)((uint8)0x01u << Millis_CTRL2_IRQ_SEL_SHIFT))     
    
    /* Status Register Bit Locations */
    #define Millis_STATUS_ZERO_SHIFT      0x07u  /* As defined in Register Map, part of TMRX_SR0 register */ 

    /* Status Register Interrupt Enable Bit Locations */
    #define Millis_STATUS_ZERO_INT_EN_MASK_SHIFT      (Millis_STATUS_ZERO_SHIFT - 0x04u)

    /* Status Register Bit Masks */                           
    #define Millis_STATUS_ZERO            ((uint8)((uint8)0x01u << Millis_STATUS_ZERO_SHIFT))

    /* Status Register Interrupt Bit Masks*/
    #define Millis_STATUS_ZERO_INT_EN_MASK       ((uint8)((uint8)Millis_STATUS_ZERO >> 0x04u))
    
    /*RT1 Synch Constants: Applicable for PSoC3 and PSoC5LP */
    #define Millis_RT1_SHIFT            0x04u
    #define Millis_RT1_MASK             ((uint8)((uint8)0x03u << Millis_RT1_SHIFT))  /* Sync TC and CMP bit masks */
    #define Millis_SYNC                 ((uint8)((uint8)0x03u << Millis_RT1_SHIFT))
    #define Millis_SYNCDSI_SHIFT        0x00u
    #define Millis_SYNCDSI_MASK         ((uint8)((uint8)0x0Fu << Millis_SYNCDSI_SHIFT)) /* Sync all DSI inputs */
    #define Millis_SYNCDSI_EN           ((uint8)((uint8)0x0Fu << Millis_SYNCDSI_SHIFT)) /* Sync all DSI inputs */
    
#else /* !Millis_UsingFixedFunction */
    #define Millis_STATUS               (* (reg8 *) Millis_CounterUDB_sSTSReg_stsreg__STATUS_REG )
    #define Millis_STATUS_PTR           (  (reg8 *) Millis_CounterUDB_sSTSReg_stsreg__STATUS_REG )
    #define Millis_STATUS_MASK          (* (reg8 *) Millis_CounterUDB_sSTSReg_stsreg__MASK_REG )
    #define Millis_STATUS_MASK_PTR      (  (reg8 *) Millis_CounterUDB_sSTSReg_stsreg__MASK_REG )
    #define Millis_STATUS_AUX_CTRL      (*(reg8 *) Millis_CounterUDB_sSTSReg_stsreg__STATUS_AUX_CTL_REG)
    #define Millis_STATUS_AUX_CTRL_PTR  ( (reg8 *) Millis_CounterUDB_sSTSReg_stsreg__STATUS_AUX_CTL_REG)
    #define Millis_CONTROL              (* (reg8 *) Millis_CounterUDB_sCTRLReg_ctrlreg__CONTROL_REG )
    #define Millis_CONTROL_PTR          (  (reg8 *) Millis_CounterUDB_sCTRLReg_ctrlreg__CONTROL_REG )


    /********************************
    *    Constants
    ********************************/
    /* Control Register Bit Locations */
    #define Millis_CTRL_CAPMODE0_SHIFT    0x03u       /* As defined by Verilog Implementation */
    #define Millis_CTRL_RESET_SHIFT       0x06u       /* As defined by Verilog Implementation */
    #define Millis_CTRL_ENABLE_SHIFT      0x07u       /* As defined by Verilog Implementation */
    /* Control Register Bit Masks */
    #define Millis_CTRL_CMPMODE_MASK      0x07u 
    #define Millis_CTRL_CAPMODE_MASK      0x03u  
    #define Millis_CTRL_RESET             ((uint8)((uint8)0x01u << Millis_CTRL_RESET_SHIFT))  
    #define Millis_CTRL_ENABLE            ((uint8)((uint8)0x01u << Millis_CTRL_ENABLE_SHIFT)) 

    /* Status Register Bit Locations */
    #define Millis_STATUS_CMP_SHIFT       0x00u       /* As defined by Verilog Implementation */
    #define Millis_STATUS_ZERO_SHIFT      0x01u       /* As defined by Verilog Implementation */
    #define Millis_STATUS_OVERFLOW_SHIFT  0x02u       /* As defined by Verilog Implementation */
    #define Millis_STATUS_UNDERFLOW_SHIFT 0x03u       /* As defined by Verilog Implementation */
    #define Millis_STATUS_CAPTURE_SHIFT   0x04u       /* As defined by Verilog Implementation */
    #define Millis_STATUS_FIFOFULL_SHIFT  0x05u       /* As defined by Verilog Implementation */
    #define Millis_STATUS_FIFONEMP_SHIFT  0x06u       /* As defined by Verilog Implementation */
    /* Status Register Interrupt Enable Bit Locations - UDB Status Interrupt Mask match Status Bit Locations*/
    #define Millis_STATUS_CMP_INT_EN_MASK_SHIFT       Millis_STATUS_CMP_SHIFT       
    #define Millis_STATUS_ZERO_INT_EN_MASK_SHIFT      Millis_STATUS_ZERO_SHIFT      
    #define Millis_STATUS_OVERFLOW_INT_EN_MASK_SHIFT  Millis_STATUS_OVERFLOW_SHIFT  
    #define Millis_STATUS_UNDERFLOW_INT_EN_MASK_SHIFT Millis_STATUS_UNDERFLOW_SHIFT 
    #define Millis_STATUS_CAPTURE_INT_EN_MASK_SHIFT   Millis_STATUS_CAPTURE_SHIFT   
    #define Millis_STATUS_FIFOFULL_INT_EN_MASK_SHIFT  Millis_STATUS_FIFOFULL_SHIFT  
    #define Millis_STATUS_FIFONEMP_INT_EN_MASK_SHIFT  Millis_STATUS_FIFONEMP_SHIFT  
    /* Status Register Bit Masks */                
    #define Millis_STATUS_CMP             ((uint8)((uint8)0x01u << Millis_STATUS_CMP_SHIFT))  
    #define Millis_STATUS_ZERO            ((uint8)((uint8)0x01u << Millis_STATUS_ZERO_SHIFT)) 
    #define Millis_STATUS_OVERFLOW        ((uint8)((uint8)0x01u << Millis_STATUS_OVERFLOW_SHIFT)) 
    #define Millis_STATUS_UNDERFLOW       ((uint8)((uint8)0x01u << Millis_STATUS_UNDERFLOW_SHIFT)) 
    #define Millis_STATUS_CAPTURE         ((uint8)((uint8)0x01u << Millis_STATUS_CAPTURE_SHIFT)) 
    #define Millis_STATUS_FIFOFULL        ((uint8)((uint8)0x01u << Millis_STATUS_FIFOFULL_SHIFT))
    #define Millis_STATUS_FIFONEMP        ((uint8)((uint8)0x01u << Millis_STATUS_FIFONEMP_SHIFT))
    /* Status Register Interrupt Bit Masks  - UDB Status Interrupt Mask match Status Bit Locations */
    #define Millis_STATUS_CMP_INT_EN_MASK            Millis_STATUS_CMP                    
    #define Millis_STATUS_ZERO_INT_EN_MASK           Millis_STATUS_ZERO            
    #define Millis_STATUS_OVERFLOW_INT_EN_MASK       Millis_STATUS_OVERFLOW        
    #define Millis_STATUS_UNDERFLOW_INT_EN_MASK      Millis_STATUS_UNDERFLOW       
    #define Millis_STATUS_CAPTURE_INT_EN_MASK        Millis_STATUS_CAPTURE         
    #define Millis_STATUS_FIFOFULL_INT_EN_MASK       Millis_STATUS_FIFOFULL        
    #define Millis_STATUS_FIFONEMP_INT_EN_MASK       Millis_STATUS_FIFONEMP         
    

    /* StatusI Interrupt Enable bit Location in the Auxilliary Control Register */
    #define Millis_STATUS_ACTL_INT_EN     0x10u /* As defined for the ACTL Register */
    
    /* Datapath Auxillary Control Register definitions */
    #define Millis_AUX_CTRL_FIFO0_CLR         0x01u   /* As defined by Register map */
    #define Millis_AUX_CTRL_FIFO1_CLR         0x02u   /* As defined by Register map */
    #define Millis_AUX_CTRL_FIFO0_LVL         0x04u   /* As defined by Register map */
    #define Millis_AUX_CTRL_FIFO1_LVL         0x08u   /* As defined by Register map */
    #define Millis_STATUS_ACTL_INT_EN_MASK    0x10u   /* As defined for the ACTL Register */
    
#endif /* Millis_UsingFixedFunction */

#endif  /* CY_COUNTER_Millis_H */


/* [] END OF FILE */
