mlukasek/SAPI_DTR-1/SW/PSoC_Creator/DTR-1 v2 HW.cydsn/codegentemp/ADH_Reg.c

/*******************************************************************************
* File Name: ADH_Reg.c  
* Version 1.90
*
* Description:
*  This file contains API to enable firmware to read the value of a Status 
*  Register.
*
* Note:
*
********************************************************************************
* Copyright 2008-2015, Cypress Semiconductor Corporation.  All rights reserved.
* You may use this file only in accordance with the license, terms, conditions, 
* disclaimers, and limitations in the end user license agreement accompanying 
* the software package with which this file was provided.
*******************************************************************************/

#include "ADH_Reg.h"

#if !defined(ADH_Reg_sts_sts_reg__REMOVED) /* Check for removal by optimization */


/*******************************************************************************
* Function Name: ADH_Reg_Read
********************************************************************************
*
* Summary:
*  Reads the current value assigned to the Status Register.
*
* Parameters:
*  None.
*
* Return:
*  The current value in the Status Register.
*
*******************************************************************************/
uint8 ADH_Reg_Read(void) 
{ 
    return ADH_Reg_Status;
}


/*******************************************************************************
* Function Name: ADH_Reg_InterruptEnable
********************************************************************************
*
* Summary:
*  Enables the Status Register interrupt.
*
* Parameters:
*  None.
*
* Return:
*  None.
*
*******************************************************************************/
void ADH_Reg_InterruptEnable(void) 
{
    uint8 interruptState;
    interruptState = CyEnterCriticalSection();
    ADH_Reg_Status_Aux_Ctrl |= ADH_Reg_STATUS_INTR_ENBL;
    CyExitCriticalSection(interruptState);
}


/*******************************************************************************
* Function Name: ADH_Reg_InterruptDisable
********************************************************************************
*
* Summary:
*  Disables the Status Register interrupt.
*
* Parameters:
*  None.
*
* Return:
*  None.
*
*******************************************************************************/
void ADH_Reg_InterruptDisable(void) 
{
    uint8 interruptState;
    interruptState = CyEnterCriticalSection();
    ADH_Reg_Status_Aux_Ctrl &= (uint8)(~ADH_Reg_STATUS_INTR_ENBL);
    CyExitCriticalSection(interruptState);
}


/*******************************************************************************
* Function Name: ADH_Reg_WriteMask
********************************************************************************
*
* Summary:
*  Writes the current mask value assigned to the Status Register.
*
* Parameters:
*  mask:  Value to write into the mask register.
*
* Return:
*  None.
*
*******************************************************************************/
void ADH_Reg_WriteMask(uint8 mask) 
{
    #if(ADH_Reg_INPUTS < 8u)
    	mask &= ((uint8)(1u << ADH_Reg_INPUTS) - 1u);
	#endif /* End ADH_Reg_INPUTS < 8u */
    ADH_Reg_Status_Mask = mask;
}


/*******************************************************************************
* Function Name: ADH_Reg_ReadMask
********************************************************************************
*
* Summary:
*  Reads the current interrupt mask assigned to the Status Register.
*
* Parameters:
*  None.
*
* Return:
*  The value of the interrupt mask of the Status Register.
*
*******************************************************************************/
uint8 ADH_Reg_ReadMask(void) 
{
    return ADH_Reg_Status_Mask;
}

#endif /* End check for removal by optimization */


/* [] END OF FILE */
