mlukasek/SAPI_DTR-1/SW/PSoC_Creator/DTR-1 v2 HW.cydsn/codegentemp/MR.h

/*******************************************************************************
* File Name: MR.h  
* Version 2.20
*
* Description:
*  This file contains Pin function prototypes and register defines
*
* Note:
*
********************************************************************************
* Copyright 2008-2015, Cypress Semiconductor Corporation.  All rights reserved.
* You may use this file only in accordance with the license, terms, conditions, 
* disclaimers, and limitations in the end user license agreement accompanying 
* the software package with which this file was provided.
*******************************************************************************/

#if !defined(CY_PINS_MR_H) /* Pins MR_H */
#define CY_PINS_MR_H

#include "cytypes.h"
#include "cyfitter.h"
#include "cypins.h"
#include "MR_aliases.h"

/* APIs are not generated for P15[7:6] */
#if !(CY_PSOC5A &&\
	 MR__PORT == 15 && ((MR__MASK & 0xC0) != 0))


/***************************************
*        Function Prototypes             
***************************************/    

/**
* \addtogroup group_general
* @{
*/
void    MR_Write(uint8 value);
void    MR_SetDriveMode(uint8 mode);
uint8   MR_ReadDataReg(void);
uint8   MR_Read(void);
void    MR_SetInterruptMode(uint16 position, uint16 mode);
uint8   MR_ClearInterrupt(void);
/** @} general */

/***************************************
*           API Constants        
***************************************/
/**
* \addtogroup group_constants
* @{
*/
    /** \addtogroup driveMode Drive mode constants
     * \brief Constants to be passed as "mode" parameter in the MR_SetDriveMode() function.
     *  @{
     */
        #define MR_DM_ALG_HIZ         PIN_DM_ALG_HIZ
        #define MR_DM_DIG_HIZ         PIN_DM_DIG_HIZ
        #define MR_DM_RES_UP          PIN_DM_RES_UP
        #define MR_DM_RES_DWN         PIN_DM_RES_DWN
        #define MR_DM_OD_LO           PIN_DM_OD_LO
        #define MR_DM_OD_HI           PIN_DM_OD_HI
        #define MR_DM_STRONG          PIN_DM_STRONG
        #define MR_DM_RES_UPDWN       PIN_DM_RES_UPDWN
    /** @} driveMode */
/** @} group_constants */
    
/* Digital Port Constants */
#define MR_MASK               MR__MASK
#define MR_SHIFT              MR__SHIFT
#define MR_WIDTH              1u

/* Interrupt constants */
#if defined(MR__INTSTAT)
/**
* \addtogroup group_constants
* @{
*/
    /** \addtogroup intrMode Interrupt constants
     * \brief Constants to be passed as "mode" parameter in MR_SetInterruptMode() function.
     *  @{
     */
        #define MR_INTR_NONE      (uint16)(0x0000u)
        #define MR_INTR_RISING    (uint16)(0x0001u)
        #define MR_INTR_FALLING   (uint16)(0x0002u)
        #define MR_INTR_BOTH      (uint16)(0x0003u) 
    /** @} intrMode */
/** @} group_constants */

    #define MR_INTR_MASK      (0x01u) 
#endif /* (MR__INTSTAT) */


/***************************************
*             Registers        
***************************************/

/* Main Port Registers */
/* Pin State */
#define MR_PS                     (* (reg8 *) MR__PS)
/* Data Register */
#define MR_DR                     (* (reg8 *) MR__DR)
/* Port Number */
#define MR_PRT_NUM                (* (reg8 *) MR__PRT) 
/* Connect to Analog Globals */                                                  
#define MR_AG                     (* (reg8 *) MR__AG)                       
/* Analog MUX bux enable */
#define MR_AMUX                   (* (reg8 *) MR__AMUX) 
/* Bidirectional Enable */                                                        
#define MR_BIE                    (* (reg8 *) MR__BIE)
/* Bit-mask for Aliased Register Access */
#define MR_BIT_MASK               (* (reg8 *) MR__BIT_MASK)
/* Bypass Enable */
#define MR_BYP                    (* (reg8 *) MR__BYP)
/* Port wide control signals */                                                   
#define MR_CTL                    (* (reg8 *) MR__CTL)
/* Drive Modes */
#define MR_DM0                    (* (reg8 *) MR__DM0) 
#define MR_DM1                    (* (reg8 *) MR__DM1)
#define MR_DM2                    (* (reg8 *) MR__DM2) 
/* Input Buffer Disable Override */
#define MR_INP_DIS                (* (reg8 *) MR__INP_DIS)
/* LCD Common or Segment Drive */
#define MR_LCD_COM_SEG            (* (reg8 *) MR__LCD_COM_SEG)
/* Enable Segment LCD */
#define MR_LCD_EN                 (* (reg8 *) MR__LCD_EN)
/* Slew Rate Control */
#define MR_SLW                    (* (reg8 *) MR__SLW)

/* DSI Port Registers */
/* Global DSI Select Register */
#define MR_PRTDSI__CAPS_SEL       (* (reg8 *) MR__PRTDSI__CAPS_SEL) 
/* Double Sync Enable */
#define MR_PRTDSI__DBL_SYNC_IN    (* (reg8 *) MR__PRTDSI__DBL_SYNC_IN) 
/* Output Enable Select Drive Strength */
#define MR_PRTDSI__OE_SEL0        (* (reg8 *) MR__PRTDSI__OE_SEL0) 
#define MR_PRTDSI__OE_SEL1        (* (reg8 *) MR__PRTDSI__OE_SEL1) 
/* Port Pin Output Select Registers */
#define MR_PRTDSI__OUT_SEL0       (* (reg8 *) MR__PRTDSI__OUT_SEL0) 
#define MR_PRTDSI__OUT_SEL1       (* (reg8 *) MR__PRTDSI__OUT_SEL1) 
/* Sync Output Enable Registers */
#define MR_PRTDSI__SYNC_OUT       (* (reg8 *) MR__PRTDSI__SYNC_OUT) 

/* SIO registers */
#if defined(MR__SIO_CFG)
    #define MR_SIO_HYST_EN        (* (reg8 *) MR__SIO_HYST_EN)
    #define MR_SIO_REG_HIFREQ     (* (reg8 *) MR__SIO_REG_HIFREQ)
    #define MR_SIO_CFG            (* (reg8 *) MR__SIO_CFG)
    #define MR_SIO_DIFF           (* (reg8 *) MR__SIO_DIFF)
#endif /* (MR__SIO_CFG) */

/* Interrupt Registers */
#if defined(MR__INTSTAT)
    #define MR_INTSTAT            (* (reg8 *) MR__INTSTAT)
    #define MR_SNAP               (* (reg8 *) MR__SNAP)
    
	#define MR_0_INTTYPE_REG 		(* (reg8 *) MR__0__INTTYPE)
#endif /* (MR__INTSTAT) */

#endif /* CY_PSOC5A... */

#endif /*  CY_PINS_MR_H */


/* [] END OF FILE */
