mlukasek/SAPI_DTR-1/SW/PSoC_Creator/DTR-1 v2 HW.cydsn/codegentemp/M1_Int.h

/*******************************************************************************
* File Name: M1_Int.h
* Version 1.71
*
*  Description:
*   Provides the function definitions for the Interrupt Controller.
*
*
********************************************************************************
* Copyright 2008-2015, Cypress Semiconductor Corporation.  All rights reserved.
* You may use this file only in accordance with the license, terms, conditions, 
* disclaimers, and limitations in the end user license agreement accompanying 
* the software package with which this file was provided.
*******************************************************************************/
#if !defined(CY_ISR_M1_Int_H)
#define CY_ISR_M1_Int_H


#include <cytypes.h>
#include <cyfitter.h>

/* Interrupt Controller API. */
void M1_Int_Start(void);
void M1_Int_StartEx(cyisraddress address);
void M1_Int_Stop(void);

CY_ISR_PROTO(M1_Int_Interrupt);

void M1_Int_SetVector(cyisraddress address);
cyisraddress M1_Int_GetVector(void);

void M1_Int_SetPriority(uint8 priority);
uint8 M1_Int_GetPriority(void);

void M1_Int_Enable(void);
uint8 M1_Int_GetState(void);
void M1_Int_Disable(void);

void M1_Int_SetPending(void);
void M1_Int_ClearPending(void);


/* Interrupt Controller Constants */

/* Address of the INTC.VECT[x] register that contains the Address of the M1_Int ISR. */
#define M1_Int_INTC_VECTOR            ((reg32 *) M1_Int__INTC_VECT)

/* Address of the M1_Int ISR priority. */
#define M1_Int_INTC_PRIOR             ((reg8 *) M1_Int__INTC_PRIOR_REG)

/* Priority of the M1_Int interrupt. */
#define M1_Int_INTC_PRIOR_NUMBER      M1_Int__INTC_PRIOR_NUM

/* Address of the INTC.SET_EN[x] byte to bit enable M1_Int interrupt. */
#define M1_Int_INTC_SET_EN            ((reg32 *) M1_Int__INTC_SET_EN_REG)

/* Address of the INTC.CLR_EN[x] register to bit clear the M1_Int interrupt. */
#define M1_Int_INTC_CLR_EN            ((reg32 *) M1_Int__INTC_CLR_EN_REG)

/* Address of the INTC.SET_PD[x] register to set the M1_Int interrupt state to pending. */
#define M1_Int_INTC_SET_PD            ((reg32 *) M1_Int__INTC_SET_PD_REG)

/* Address of the INTC.CLR_PD[x] register to clear the M1_Int interrupt. */
#define M1_Int_INTC_CLR_PD            ((reg32 *) M1_Int__INTC_CLR_PD_REG)


#endif /* CY_ISR_M1_Int_H */


/* [] END OF FILE */
