mlukasek/SAPI_DTR-1/SW/PSoC_Creator/DTR-1 v2 HW.cydsn/codegentemp/ADH_Reg.h

/*******************************************************************************
* File Name: ADH_Reg.h  
* Version 1.90
*
* Description:
*  This file containts Status Register function prototypes and register defines
*
* Note:
*
********************************************************************************
* Copyright 2008-2015, Cypress Semiconductor Corporation.  All rights reserved.
* You may use this file only in accordance with the license, terms, conditions, 
* disclaimers, and limitations in the end user license agreement accompanying 
* the software package with which this file was provided.
*******************************************************************************/

#if !defined(CY_STATUS_REG_ADH_Reg_H) /* CY_STATUS_REG_ADH_Reg_H */
#define CY_STATUS_REG_ADH_Reg_H

#include "cyfitter.h"

#if ((CYDEV_CHIP_FAMILY_USED == CYDEV_CHIP_FAMILY_PSOC3) || \
     (CYDEV_CHIP_FAMILY_USED == CYDEV_CHIP_FAMILY_PSOC4) || \
     (CYDEV_CHIP_FAMILY_USED == CYDEV_CHIP_FAMILY_PSOC5))
    #include "cytypes.h"
    #include "CyLib.h"
#else
    #include "syslib/cy_syslib.h"
#endif

    
/***************************************
*     Data Struct Definitions
***************************************/

/* Sleep Mode API Support */
typedef struct
{
    uint8 statusState;

} ADH_Reg_BACKUP_STRUCT;


/***************************************
*        Function Prototypes
***************************************/

uint8 ADH_Reg_Read(void) ;
void ADH_Reg_InterruptEnable(void) ;
void ADH_Reg_InterruptDisable(void) ;
void ADH_Reg_WriteMask(uint8 mask) ;
uint8 ADH_Reg_ReadMask(void) ;


/***************************************
*           API Constants
***************************************/

#define ADH_Reg_STATUS_INTR_ENBL    0x10u


/***************************************
*         Parameter Constants
***************************************/

/* Status Register Inputs */
#define ADH_Reg_INPUTS              8


/***************************************
*             Registers
***************************************/

/* Status Register */
#define ADH_Reg_Status             (* (reg8 *) ADH_Reg_sts_sts_reg__STATUS_REG )
#define ADH_Reg_Status_PTR         (  (reg8 *) ADH_Reg_sts_sts_reg__STATUS_REG )
#define ADH_Reg_Status_Mask        (* (reg8 *) ADH_Reg_sts_sts_reg__MASK_REG )
#define ADH_Reg_Status_Aux_Ctrl    (* (reg8 *) ADH_Reg_sts_sts_reg__STATUS_AUX_CTL_REG )

#endif /* End CY_STATUS_REG_ADH_Reg_H */


/* [] END OF FILE */
