mlukasek/SAPI_DTR-1/SW/PSoC_Creator/DTR-1 v2 HW.cydsn/codegentemp/BusDta.c

/*******************************************************************************
* File Name: BusDta.c  
* Version 1.80
*
* Description:
*  This file contains API to enable firmware control of a Control Register.
*
* Note:
*
********************************************************************************
* Copyright 2008-2015, Cypress Semiconductor Corporation.  All rights reserved.
* You may use this file only in accordance with the license, terms, conditions, 
* disclaimers, and limitations in the end user license agreement accompanying 
* the software package with which this file was provided.
*******************************************************************************/

#include "BusDta.h"

/* Check for removal by optimization */
#if !defined(BusDta_Sync_ctrl_reg__REMOVED)

    
/*******************************************************************************
* Function Name: BusDta_Write
********************************************************************************
*
* Summary:
*  Write a byte to the Control Register.
*
* Parameters:
*  control:  The value to be assigned to the Control Register.
*
* Return:
*  None.
*
*******************************************************************************/
void BusDta_Write(uint8 control) 
{
    BusDta_Control = control;
}


/*******************************************************************************
* Function Name: BusDta_Read
********************************************************************************
*
* Summary:
*  Reads the current value assigned to the Control Register.
*
* Parameters:
*  None.
*
* Return:
*  Returns the current value in the Control Register.
*
*******************************************************************************/
uint8 BusDta_Read(void) 
{
    return BusDta_Control;
}

#endif /* End check for removal by optimization */


/* [] END OF FILE */
